OpenPawLabs/diy-guides/bb-lsm6dsv/0-overview/images/battery-1000mah-side-bend-transparent-cropped-img-4592-1.webp

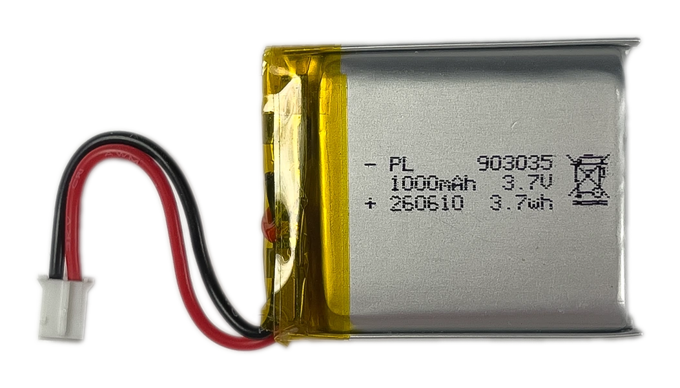
bb-lsm6dsv/0-overview/images/battery-1000mah-side-bend-transparent-cropped-img-4592-1.webp
