OpenPawLabs/diy-guides/bb-lsm6dsv/0-overview/images/battery-1000mah-side-bend-transparent-img-4592.webp

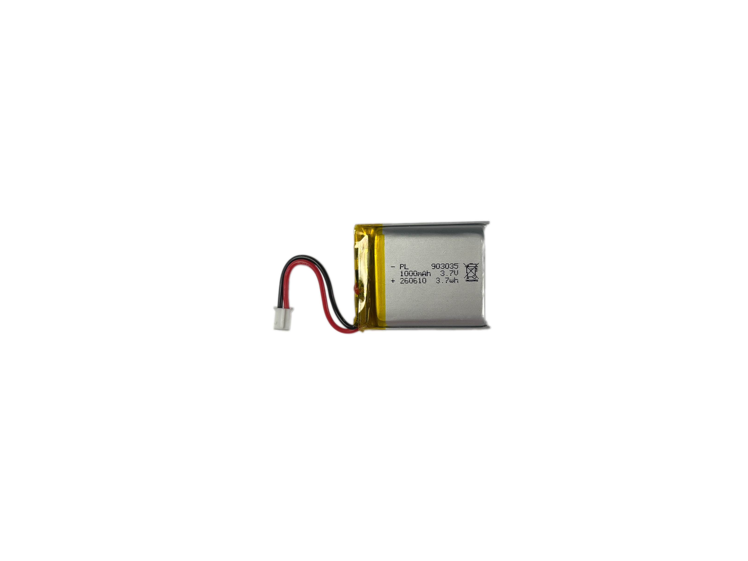
bb-lsm6dsv/0-overview/images/battery-1000mah-side-bend-transparent-img-4592.webp
