OpenPawLabs/diy-guides/bb-lsm6dsv/0-overview/images/body-strap-set-img-4863.webp

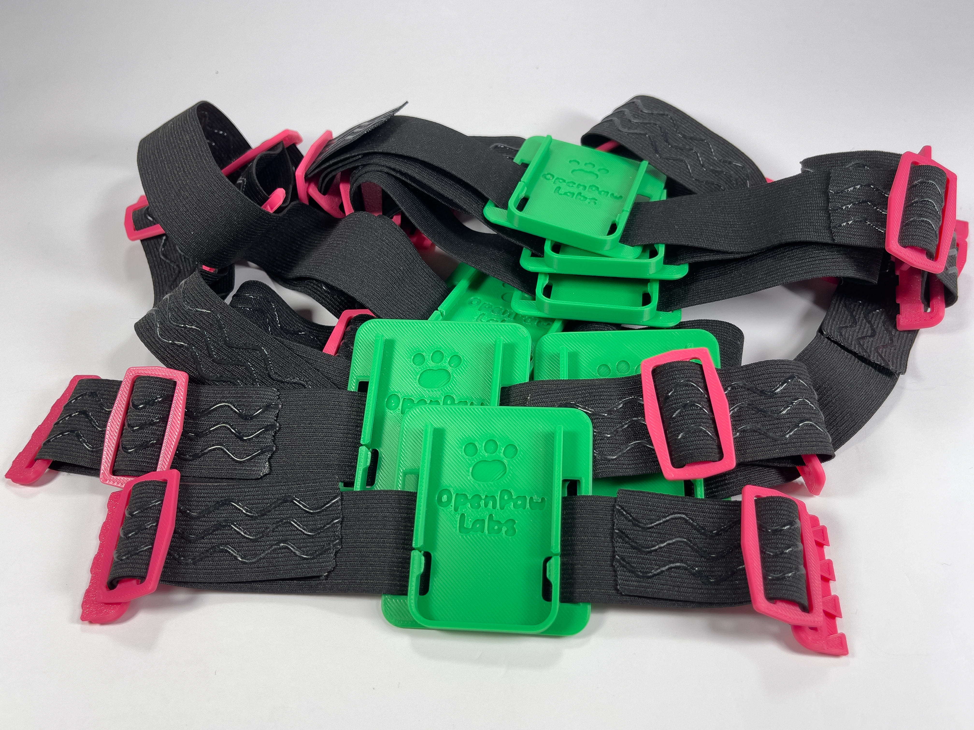
bb-lsm6dsv/0-overview/images/body-strap-set-img-4863.webp
