OpenPawLabs/diy-guides/bb-lsm6dsv/0-overview/images/dock-pcb-transparent-img-4443-1.webp

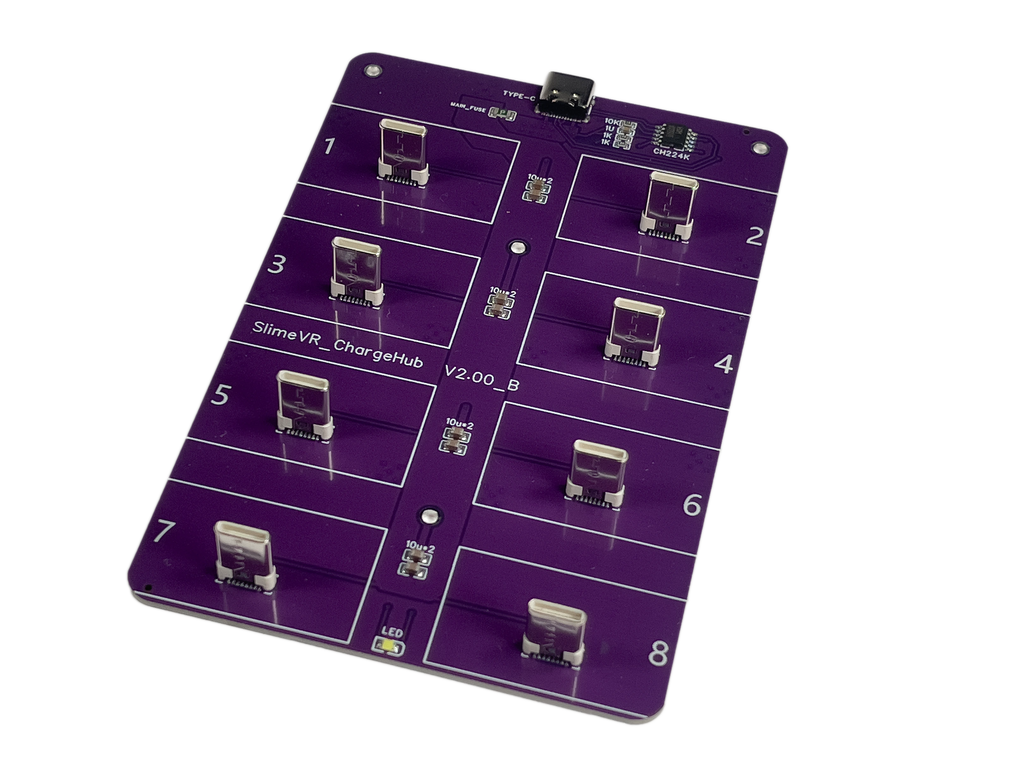
bb-lsm6dsv/0-overview/images/dock-pcb-transparent-img-4443-1.webp
