OpenPawLabs/diy-guides/bb-lsm6dsv/0-overview/images/dock-w-pcb-angled-transparent-img-4545.webp

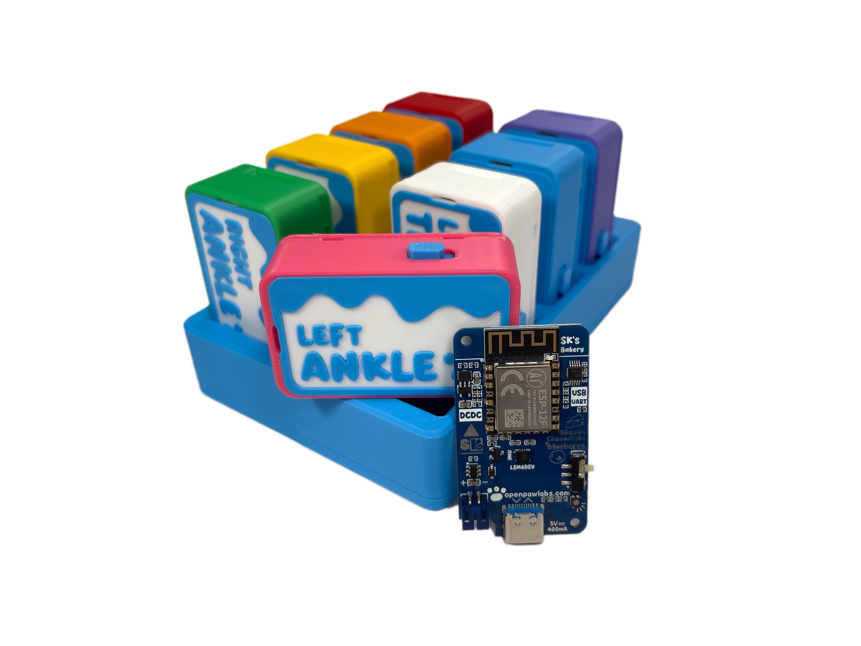
bb-lsm6dsv/0-overview/images/dock-w-pcb-angled-transparent-img-4545.webp
