OpenPawLabs/diy-guides/bb-lsm6dsv/0-overview/images/img-4400-edit.webp

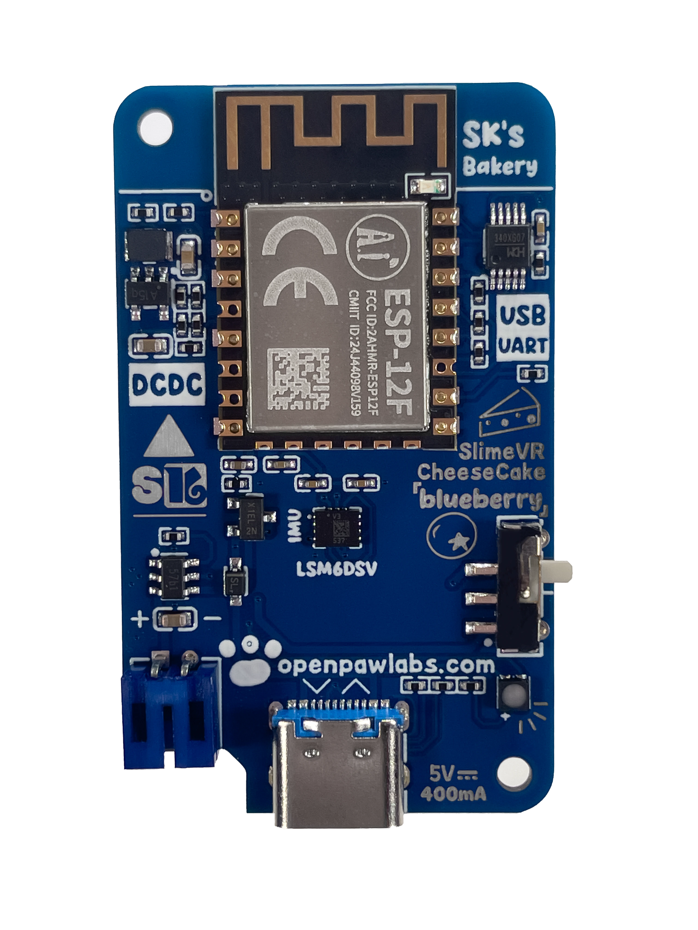
bb-lsm6dsv/0-overview/images/img-4400-edit.webp
