OpenPawLabs/diy-guides/bb-lsm6dsv/0-overview/images/img-4710.webp

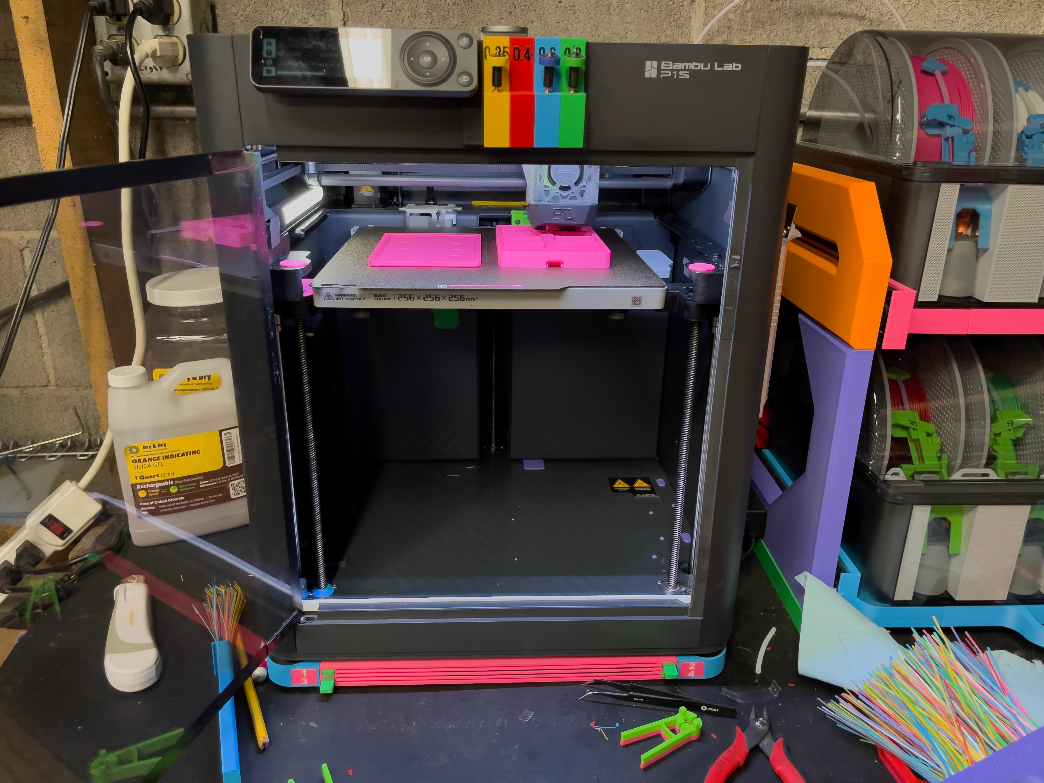
bb-lsm6dsv/0-overview/images/img-4710.webp
