OpenPawLabs/diy-guides/bb-lsm6dsv/0-overview/images/party-face-emoji-big.webp

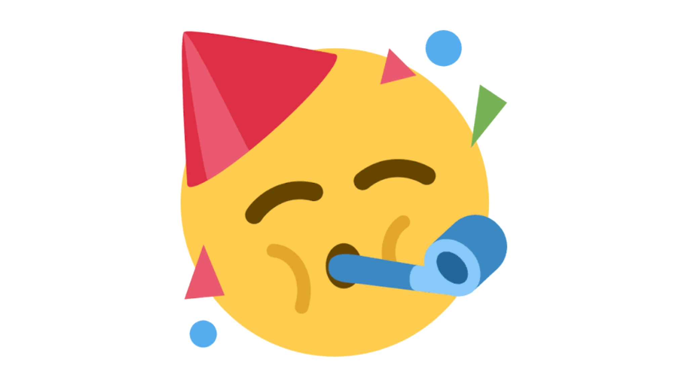
bb-lsm6dsv/0-overview/images/party-face-emoji-big.webp
