OpenPawLabs/diy-guides/bb-lsm6dsv/0-overview/images/tracker-board-transparent-1080.webp

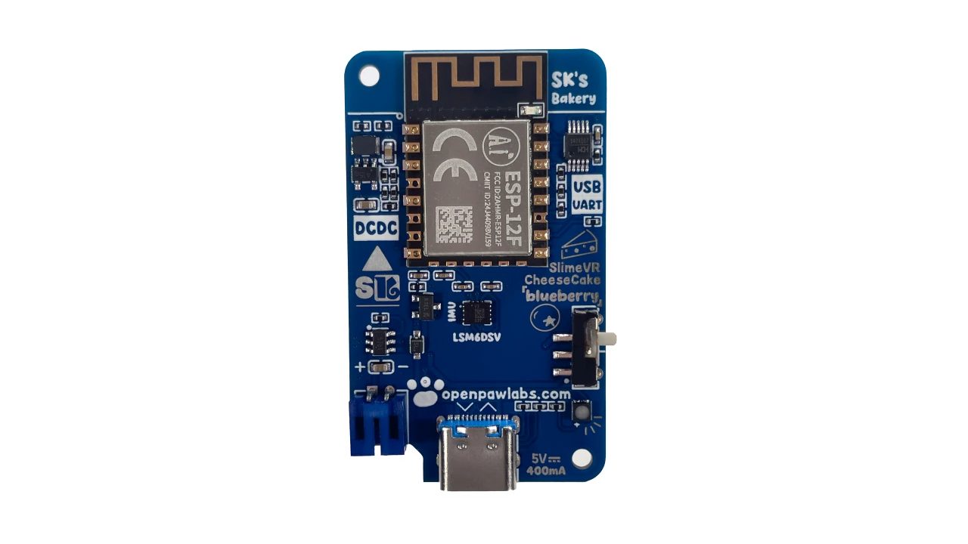
bb-lsm6dsv/0-overview/images/tracker-board-transparent-1080.webp
