OpenPawLabs/diy-guides/bb-lsm6dsv/0-overview/images/vyrovr-comfort-straps.webp

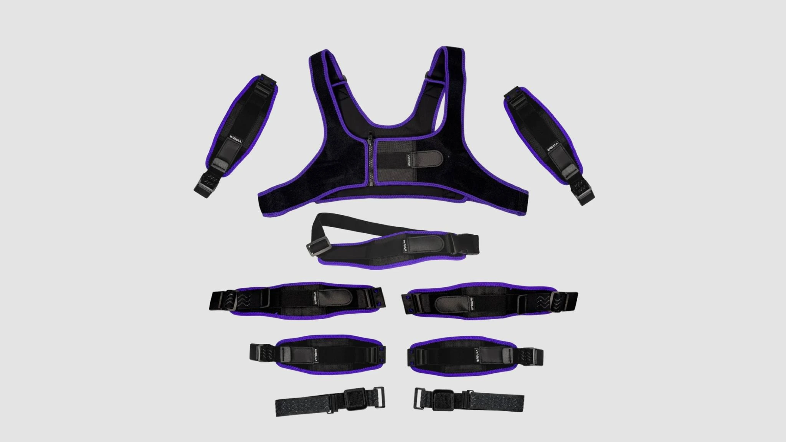
bb-lsm6dsv/0-overview/images/vyrovr-comfort-straps.webp
