OpenPawLabs/diy-guides/bb-lsm6dsv/diy-straps/images/chest-strap-3-ways-img-4871.webp

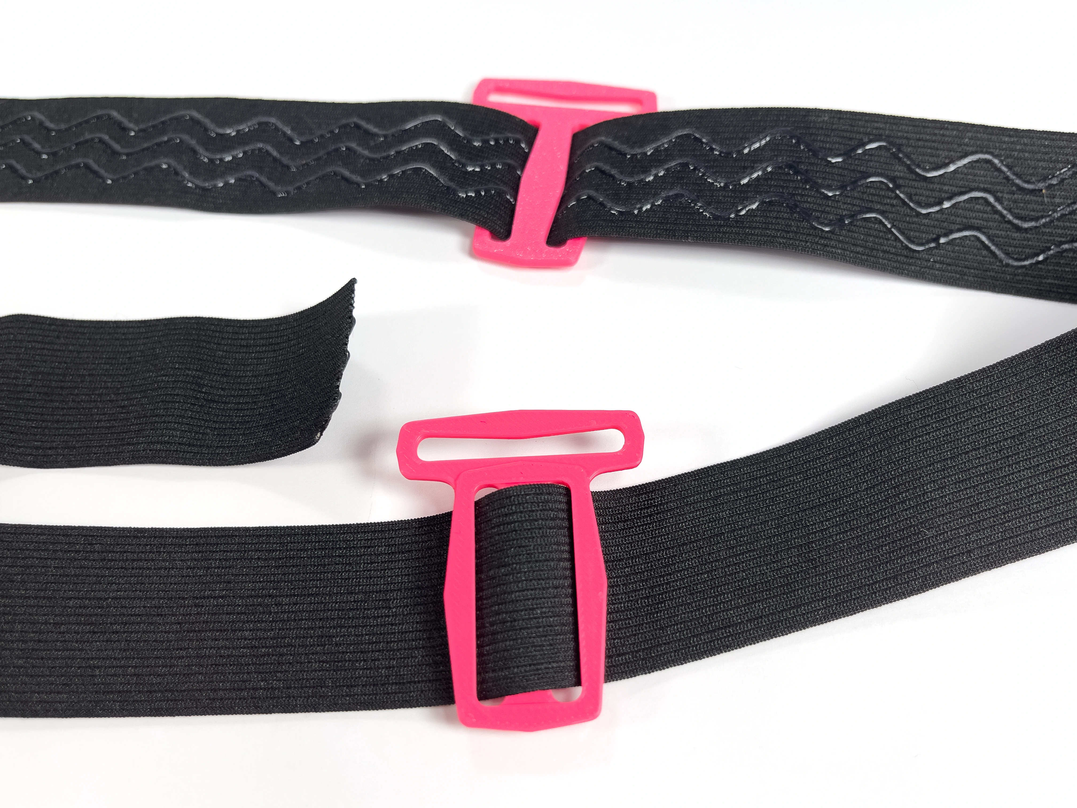
bb-lsm6dsv/diy-straps/images/chest-strap-3-ways-img-4871.webp
