OpenPawLabs/diy-guides/bb-lsm6dsv/diy-straps/images/chest-strap-3-ways-pt2-img-4873.webp

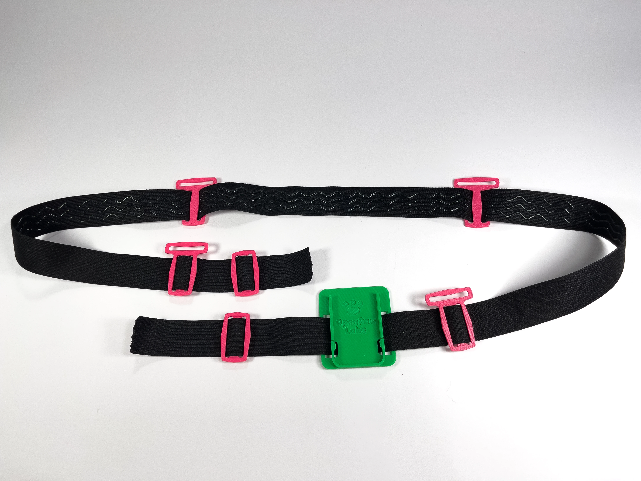
bb-lsm6dsv/diy-straps/images/chest-strap-3-ways-pt2-img-4873.webp
