OpenPawLabs/diy-guides/bb-lsm6dsv/diy-straps/images/chest-strap-balance-img-4874.webp

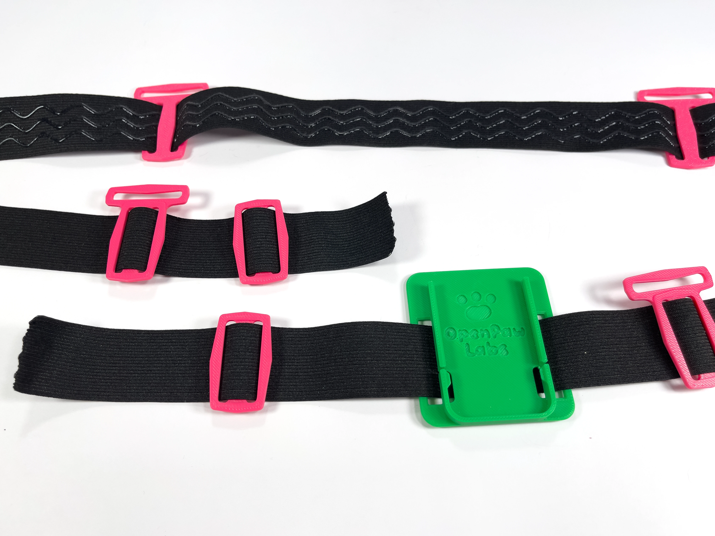
bb-lsm6dsv/diy-straps/images/chest-strap-balance-img-4874.webp
