OpenPawLabs/diy-guides/bb-lsm6dsv/diy-straps/images/chest-strap-clasps-img-4879.webp

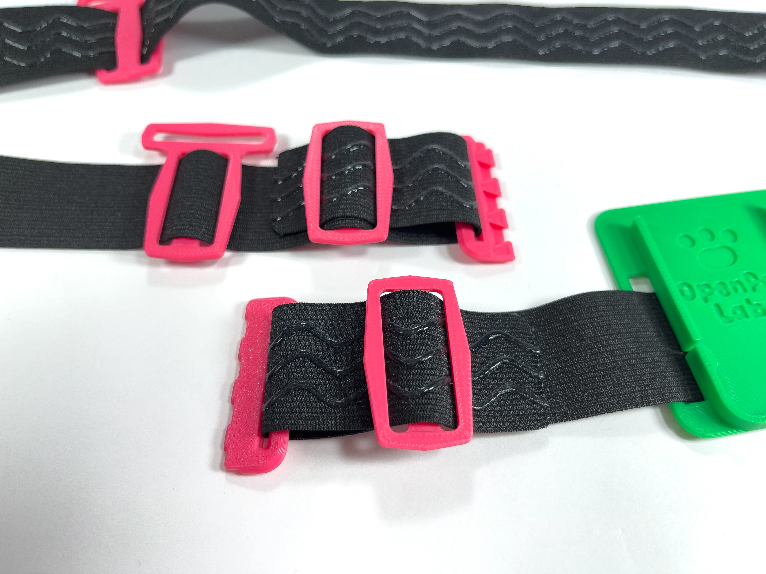
bb-lsm6dsv/diy-straps/images/chest-strap-clasps-img-4879.webp
