OpenPawLabs/diy-guides/bb-lsm6dsv/diy-straps/images/chest-straps-cut-to-length-img-4866-2.webp

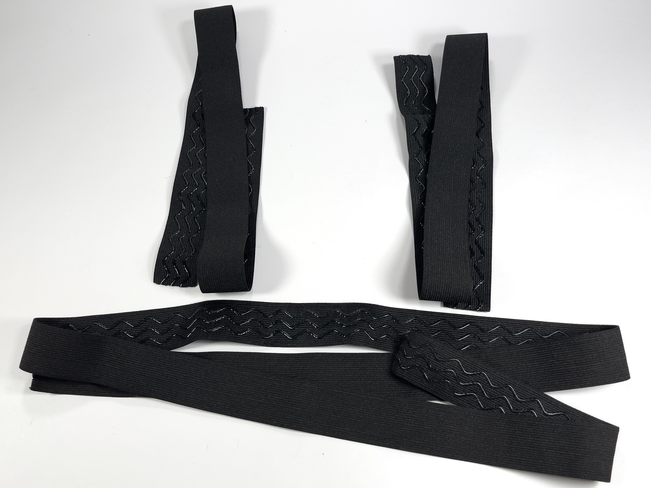
bb-lsm6dsv/diy-straps/images/chest-straps-cut-to-length-img-4866-2.webp
