OpenPawLabs/diy-guides/bb-lsm6dsv/diy-straps/images/chest-straps-pt1-img-4870.webp

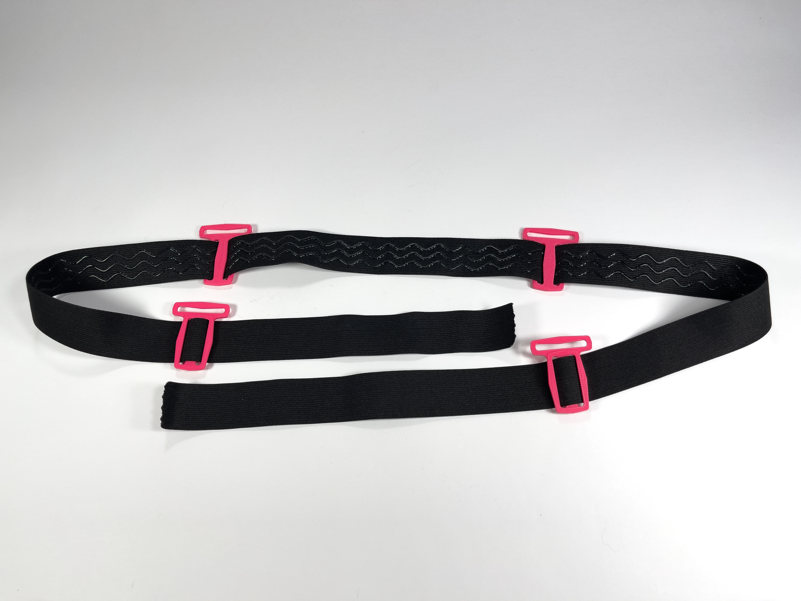
bb-lsm6dsv/diy-straps/images/chest-straps-pt1-img-4870.webp
