OpenPawLabs/diy-guides/bb-lsm6dsv/diy-straps/images/clasp-alignment-img-4828.webp

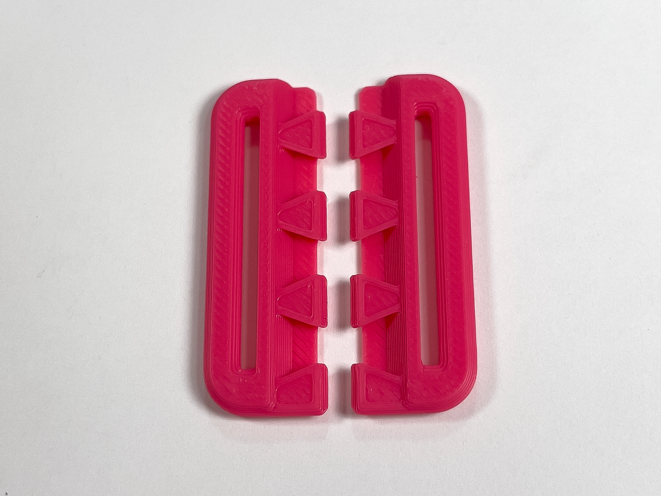
bb-lsm6dsv/diy-straps/images/clasp-alignment-img-4828.webp
