OpenPawLabs/diy-guides/bb-lsm6dsv/diy-straps/images/clasps-together-img-4861.webp

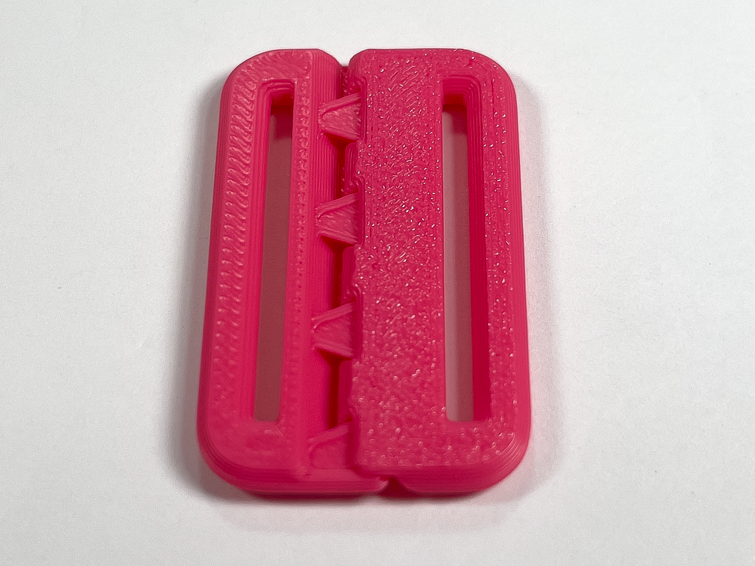
bb-lsm6dsv/diy-straps/images/clasps-together-img-4861.webp
