OpenPawLabs/diy-guides/bb-lsm6dsv/diy-straps/images/cut-to-length-img-4819.webp

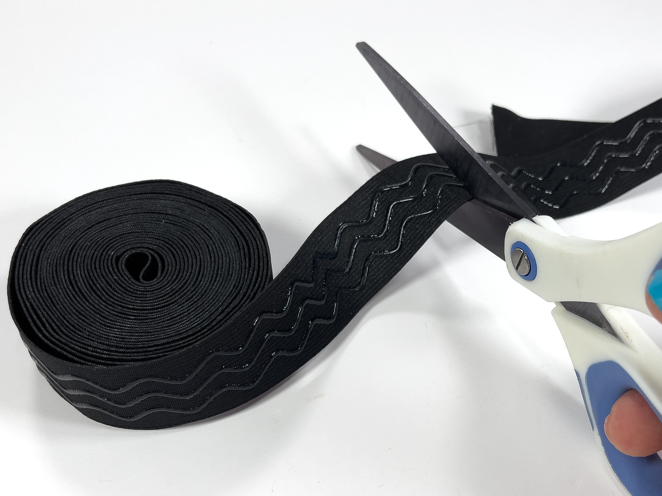
bb-lsm6dsv/diy-straps/images/cut-to-length-img-4819.webp
