OpenPawLabs/diy-guides/bb-lsm6dsv/diy-straps/images/diy-strap-set-img-4812.webp

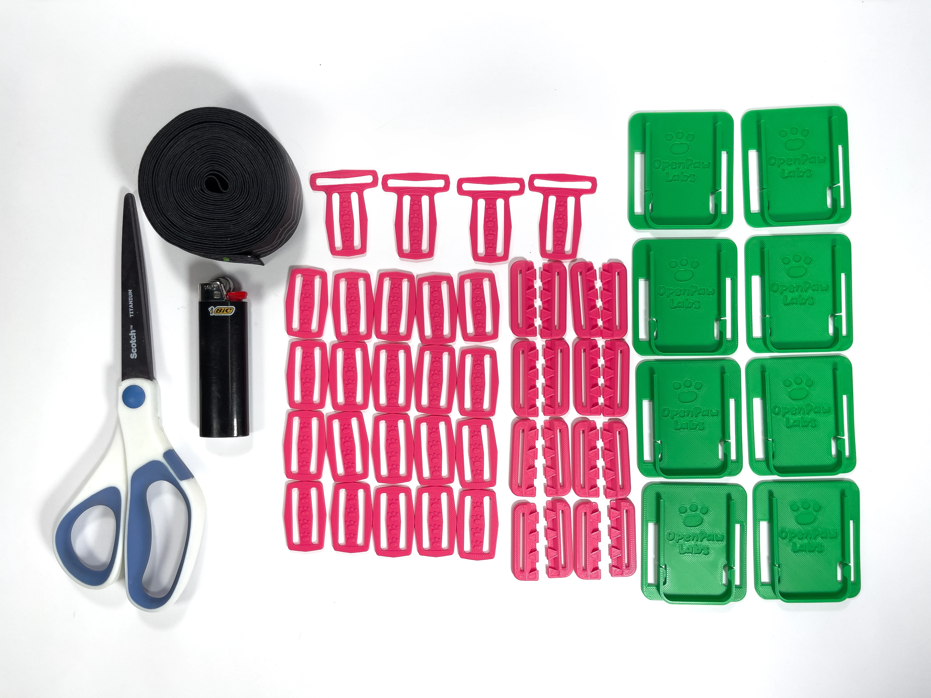
bb-lsm6dsv/diy-straps/images/diy-strap-set-img-4812.webp
