OpenPawLabs/diy-guides/bb-lsm6dsv/diy-straps/images/extra-strap-length-img-4814.webp

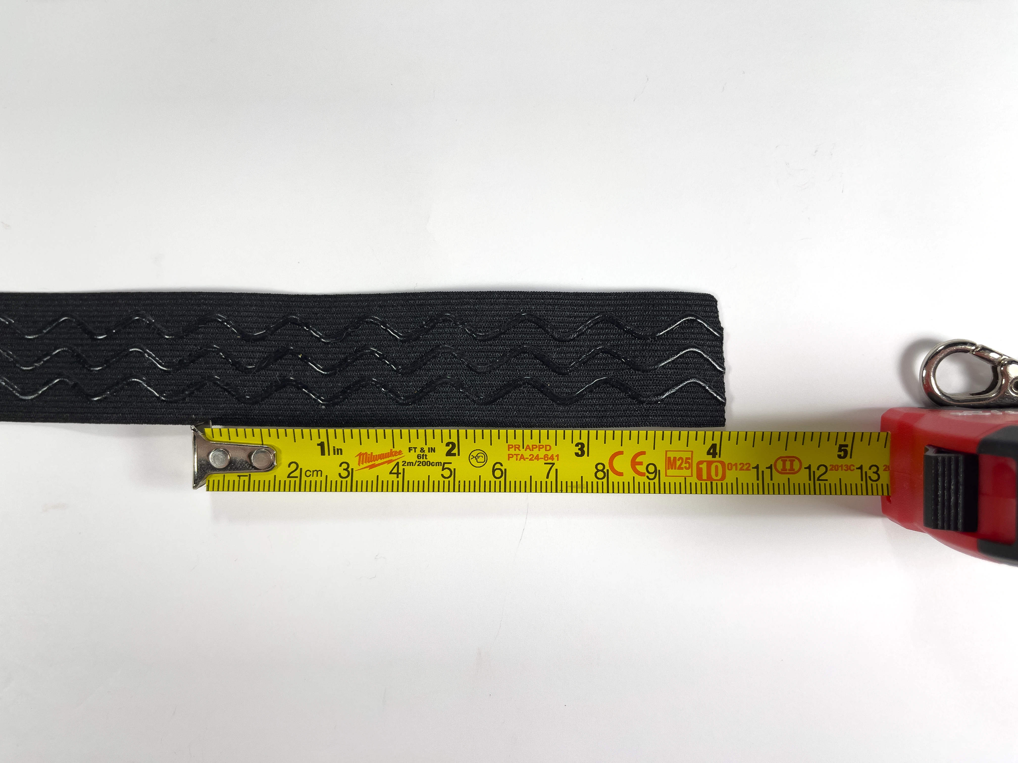
bb-lsm6dsv/diy-straps/images/extra-strap-length-img-4814.webp
