OpenPawLabs/diy-guides/bb-lsm6dsv/diy-straps/images/full-chest-strap-img-4892.webp

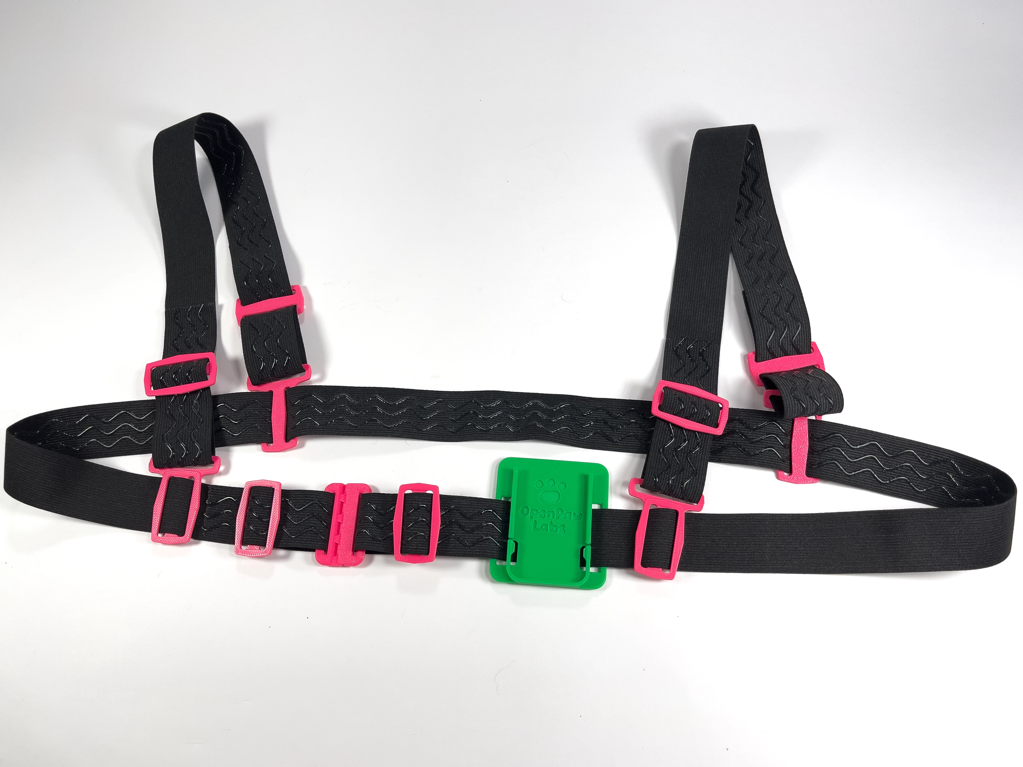
bb-lsm6dsv/diy-straps/images/full-chest-strap-img-4892.webp
