OpenPawLabs/diy-guides/bb-lsm6dsv/diy-straps/images/full-shoulder-strap-side-img-4889.webp

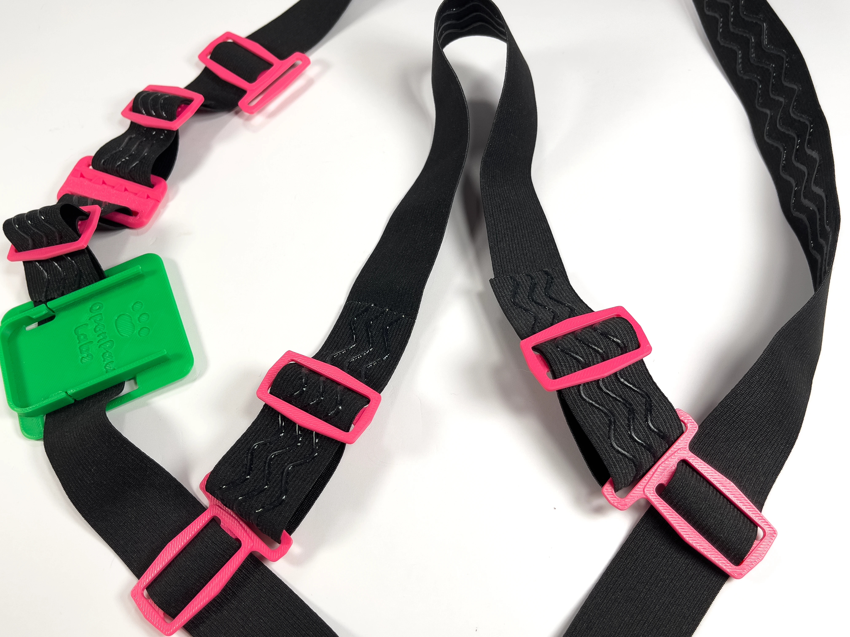
bb-lsm6dsv/diy-straps/images/full-shoulder-strap-side-img-4889.webp
