OpenPawLabs/diy-guides/bb-lsm6dsv/diy-straps/images/full-shoulder-strap-top-view-img-4890.webp

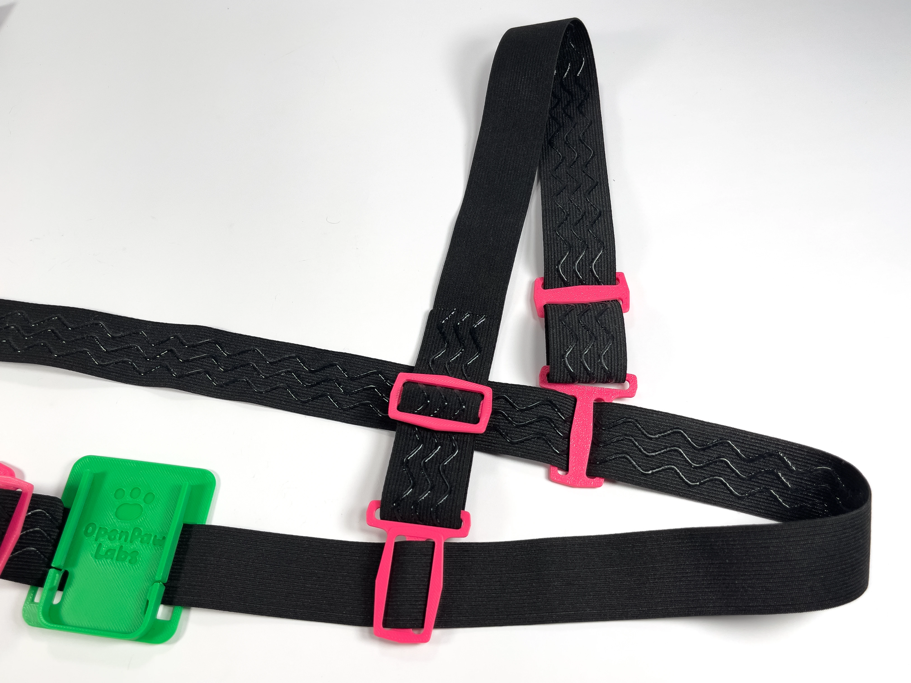
bb-lsm6dsv/diy-straps/images/full-shoulder-strap-top-view-img-4890.webp
