OpenPawLabs/diy-guides/bb-lsm6dsv/diy-straps/images/full-strap-set-img-4894.webp

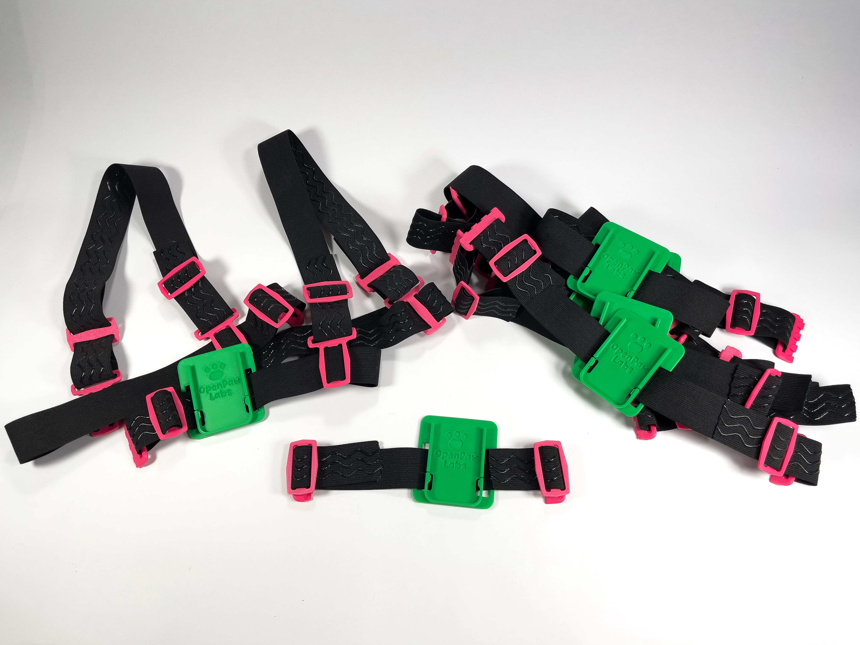
bb-lsm6dsv/diy-straps/images/full-strap-set-img-4894.webp
