OpenPawLabs/diy-guides/bb-lsm6dsv/diy-straps/images/shoulder-strap-img-4882.webp

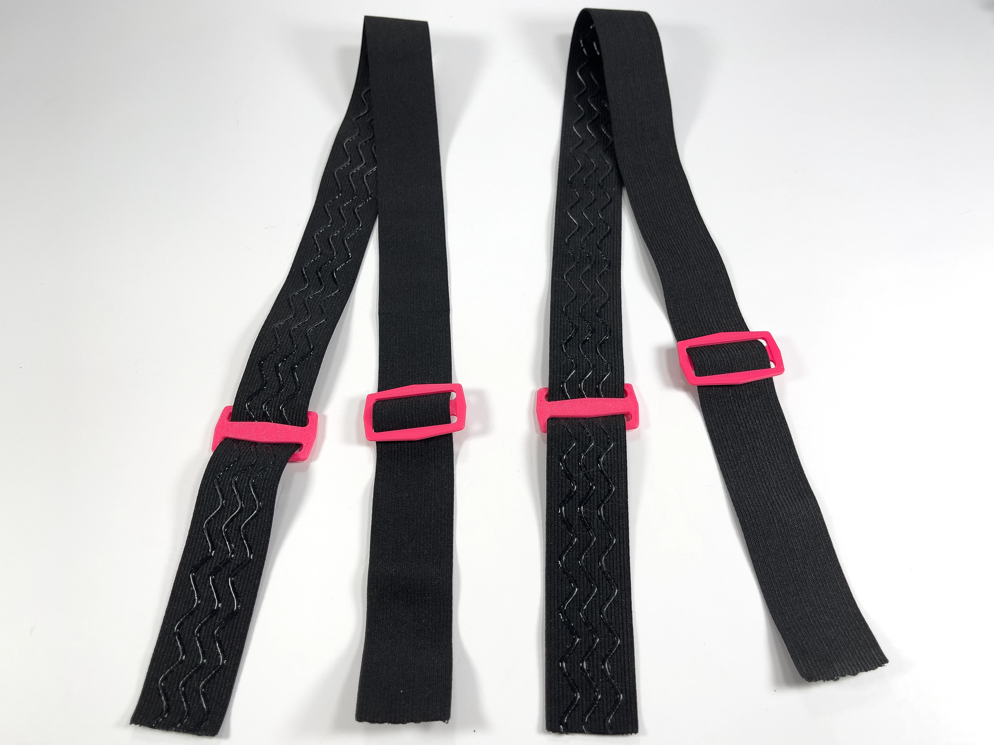
bb-lsm6dsv/diy-straps/images/shoulder-strap-img-4882.webp
