OpenPawLabs/diy-guides/bb-lsm6dsv/diy-straps/images/shoulder-strap-threading-pt1-img-4884.webp

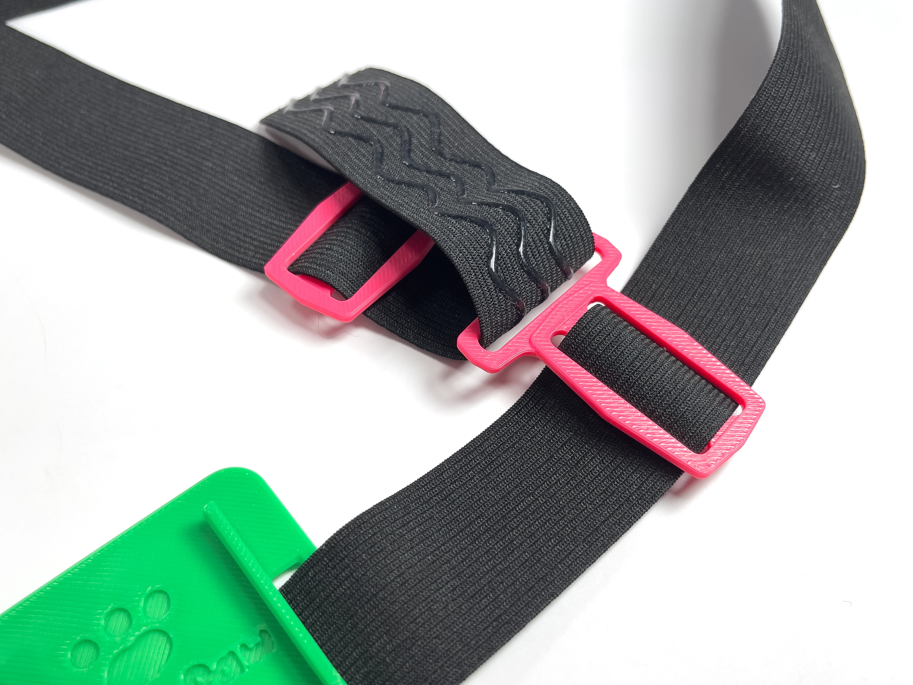
bb-lsm6dsv/diy-straps/images/shoulder-strap-threading-pt1-img-4884.webp
