OpenPawLabs/diy-guides/bb-lsm6dsv/diy-straps/images/shoulder-strap-threading-pt2-img-4886.webp

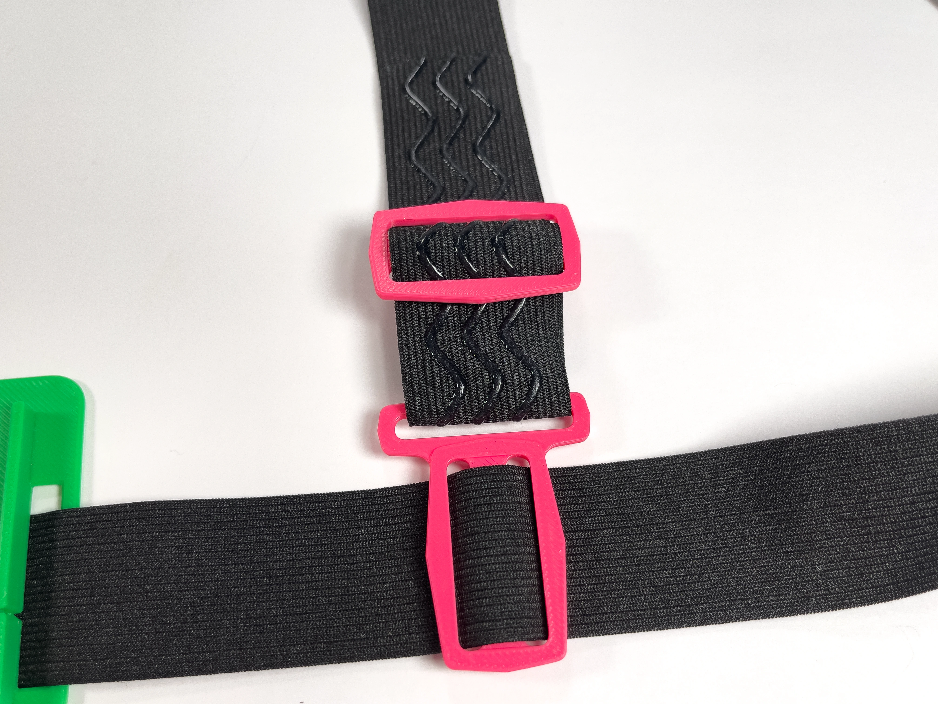
bb-lsm6dsv/diy-straps/images/shoulder-strap-threading-pt2-img-4886.webp
