OpenPawLabs/diy-guides/bb-lsm6dsv/diy-straps/images/strap-balance-closeup-img-4875.webp

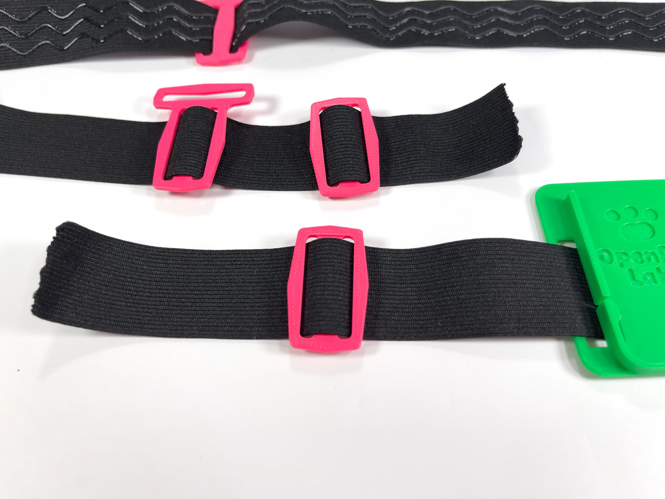
bb-lsm6dsv/diy-straps/images/strap-balance-closeup-img-4875.webp
