OpenPawLabs/diy-guides/bb-lsm6dsv/diy-straps/images/strap-clasp-threading-pt1-img-4844.webp

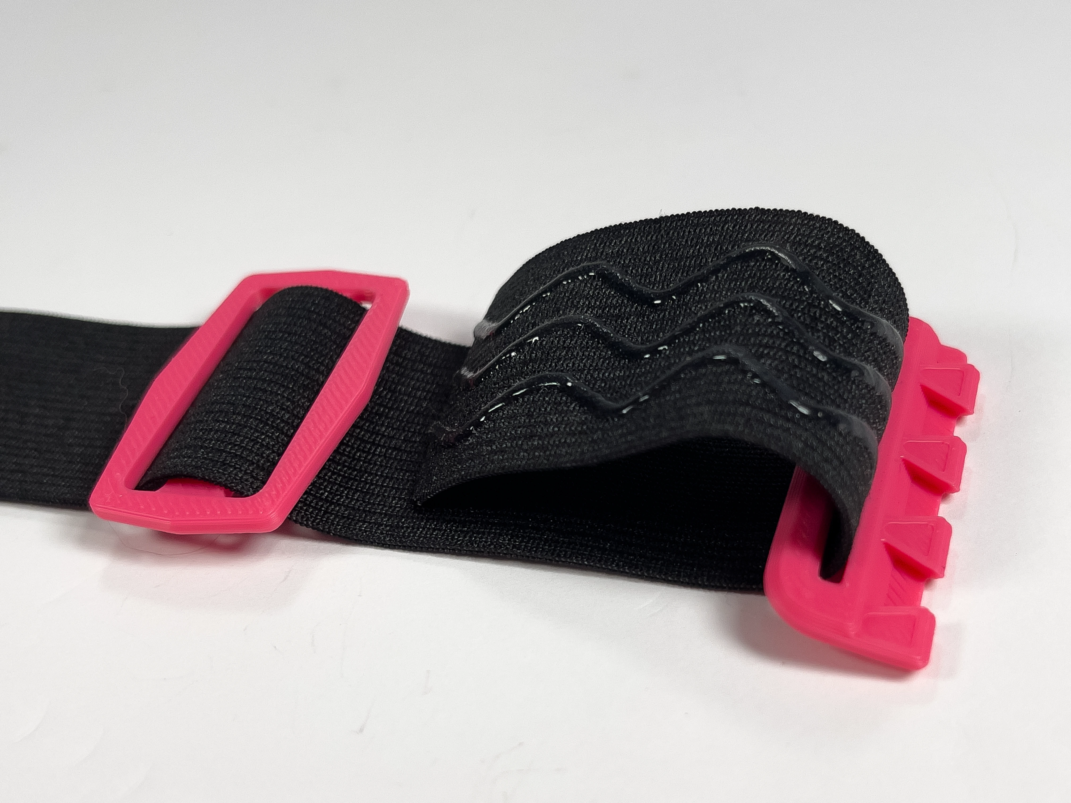
bb-lsm6dsv/diy-straps/images/strap-clasp-threading-pt1-img-4844.webp
