OpenPawLabs/diy-guides/bb-lsm6dsv/diy-straps/images/strap-clasp-two-img-4852.webp

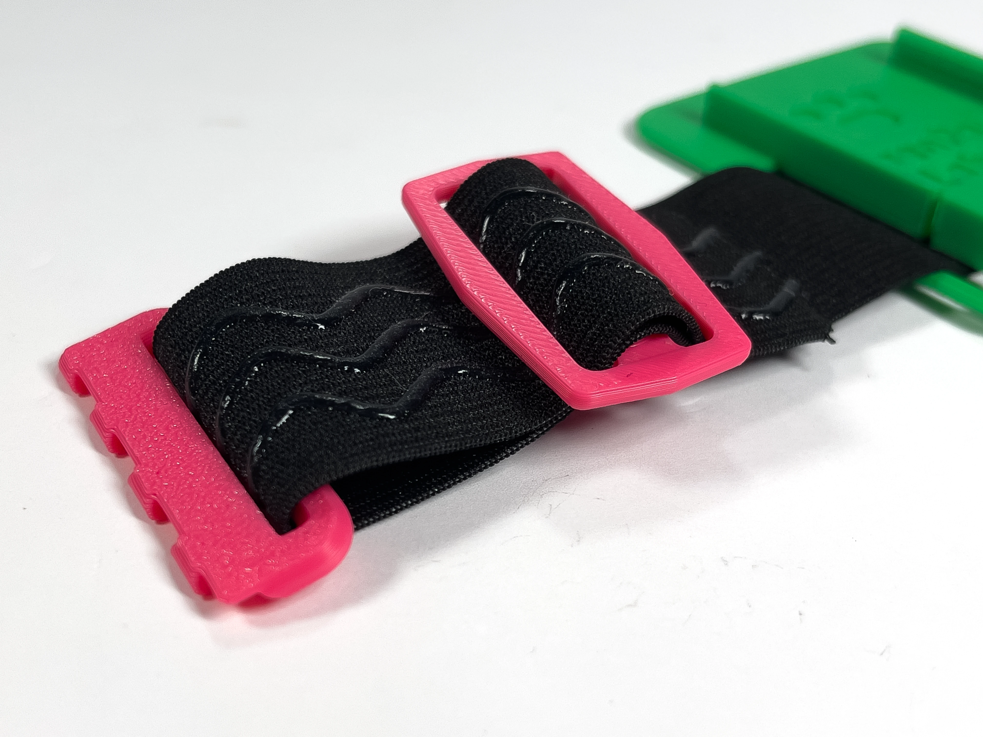
bb-lsm6dsv/diy-straps/images/strap-clasp-two-img-4852.webp
