OpenPawLabs/diy-guides/bb-lsm6dsv/diy-straps/images/strap-cut-to-length-frayed-img-4822.webp

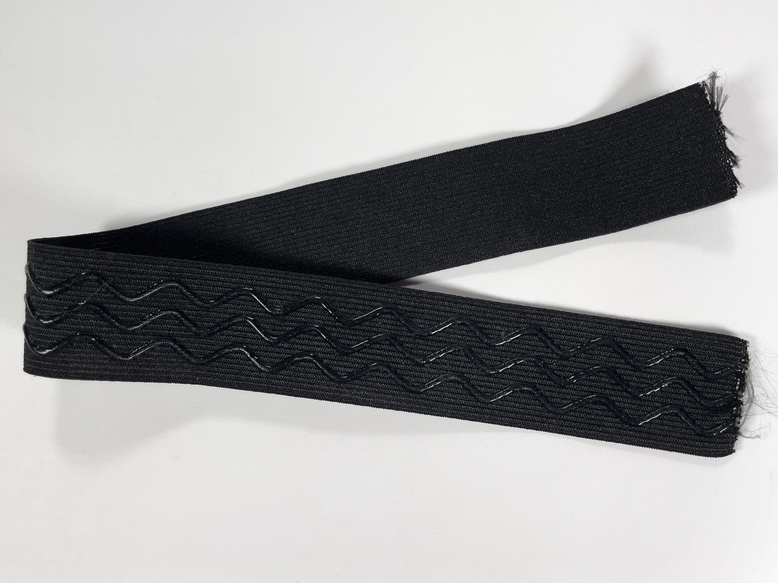
bb-lsm6dsv/diy-straps/images/strap-cut-to-length-frayed-img-4822.webp
