OpenPawLabs/diy-guides/bb-lsm6dsv/diy-straps/images/strap-standing-img-4857.webp

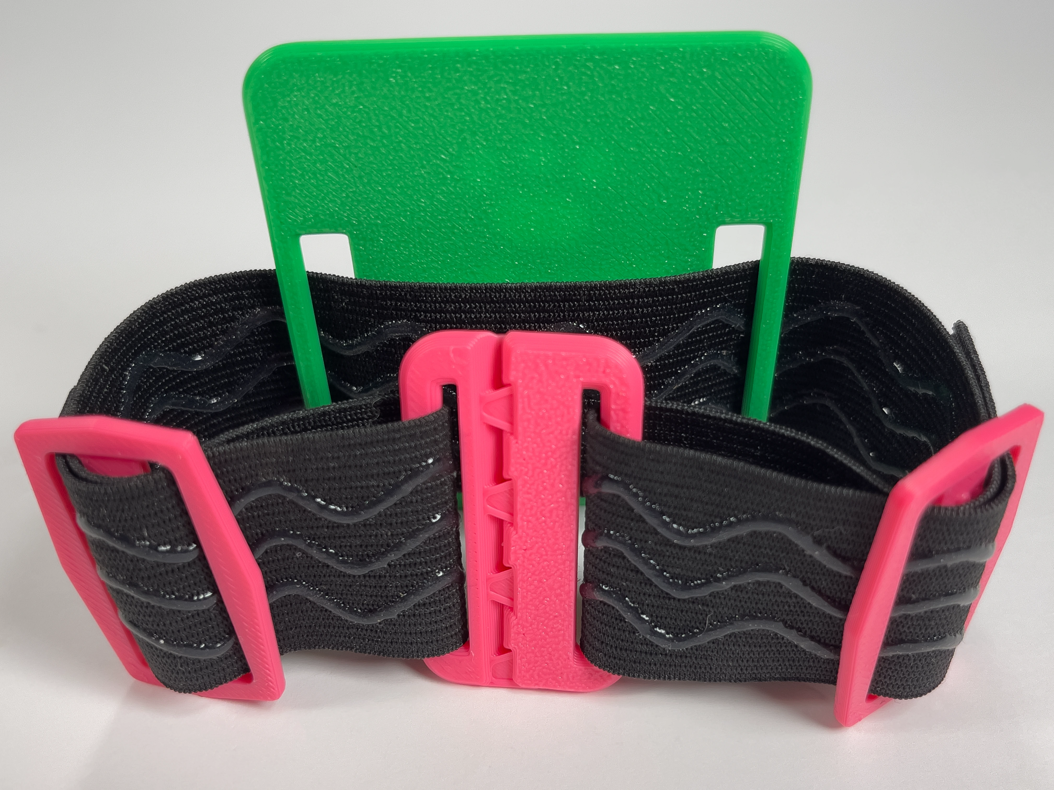
bb-lsm6dsv/diy-straps/images/strap-standing-img-4857.webp
