OpenPawLabs/diy-guides/bb-lsm6dsv/diy-straps/images/strap-threading-img-4850.webp

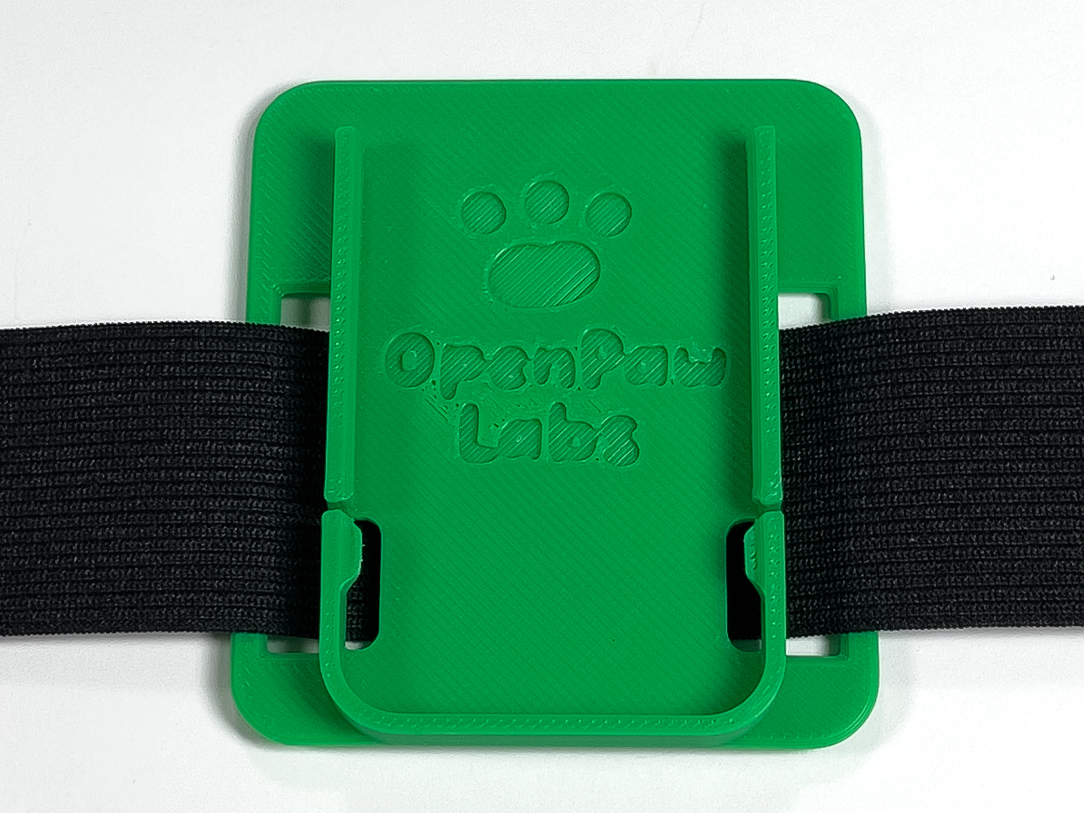
bb-lsm6dsv/diy-straps/images/strap-threading-img-4850.webp
