OpenPawLabs/diy-guides/bb-lsm6dsv/diy-straps/images/strap-threading-pt1-img-4834.webp

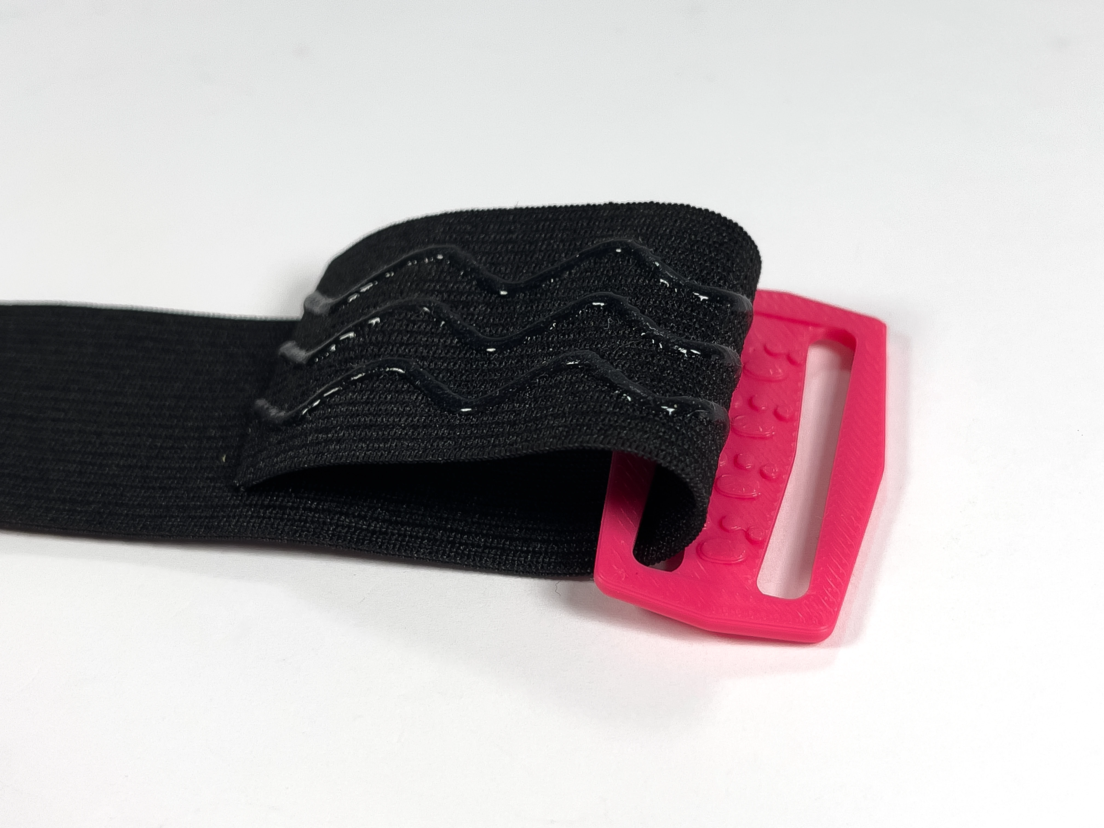
bb-lsm6dsv/diy-straps/images/strap-threading-pt1-img-4834.webp
