OpenPawLabs/diy-guides/bb-lsm6dsv/diy-straps/images/strap-threading-pt2-img-4839.webp

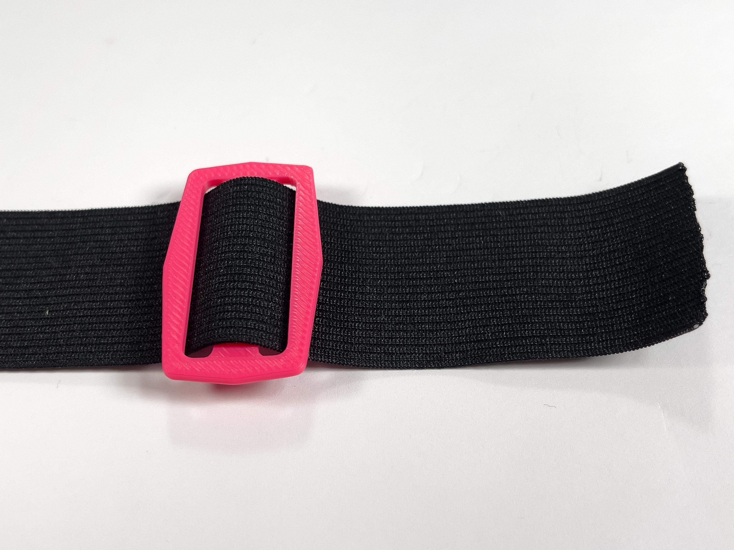
bb-lsm6dsv/diy-straps/images/strap-threading-pt2-img-4839.webp
