OpenPawLabs/diy-guides/bb-lsm6dsv/diy-straps/images/strap-threading-pt3-img-4845.webp

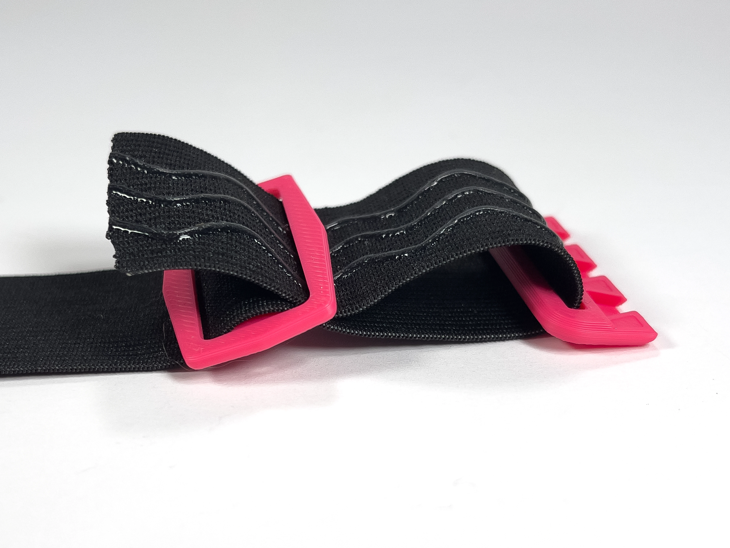
bb-lsm6dsv/diy-straps/images/strap-threading-pt3-img-4845.webp
