OpenPawLabs/diy-guides/bb-lsm6dsv/diy-straps/images/strap-threading-pt4img-4846.webp

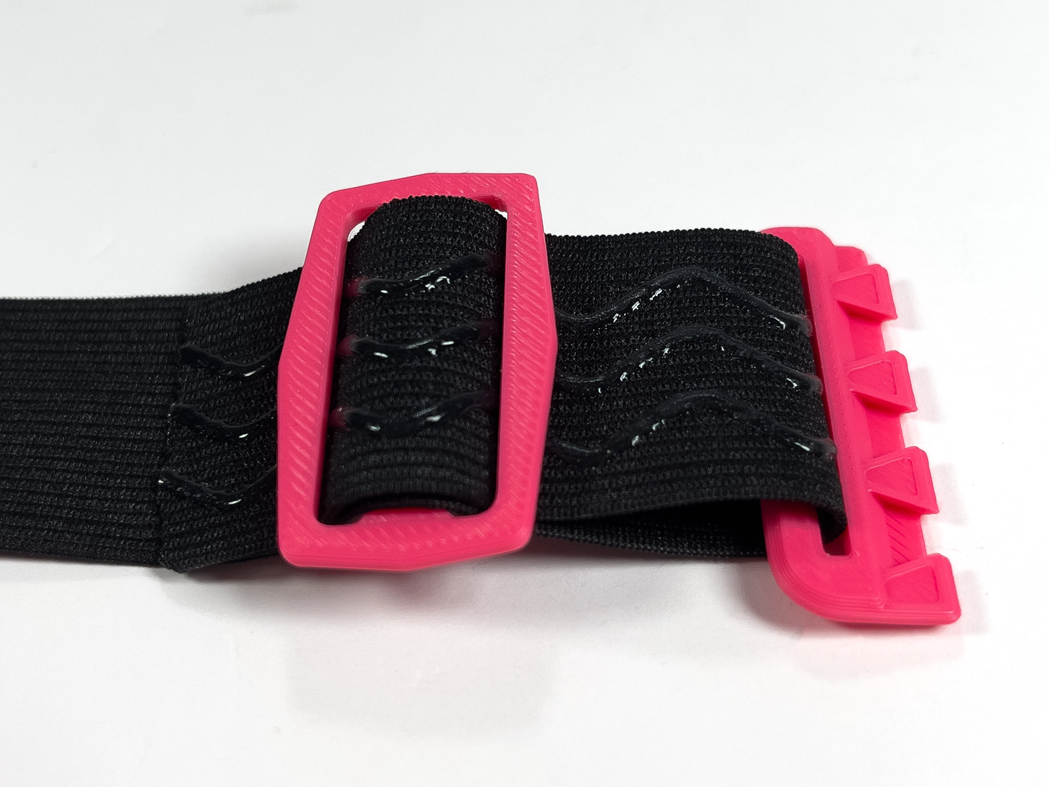
bb-lsm6dsv/diy-straps/images/strap-threading-pt4img-4846.webp
