OpenPawLabs/diy-guides/bb-lsm6dsv/diy-straps/images/sull-strap-img-4854.webp

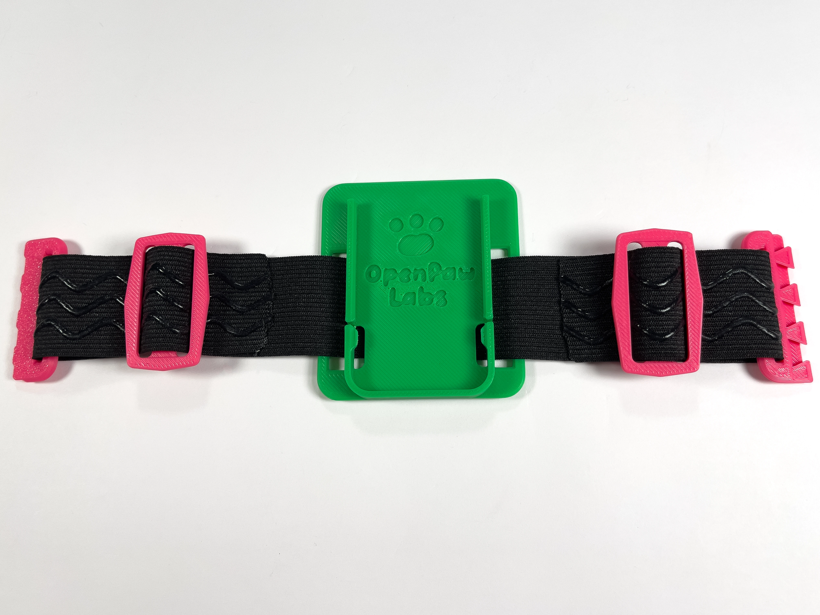
bb-lsm6dsv/diy-straps/images/sull-strap-img-4854.webp
