OpenPawLabs/diy-guides/bb-lsm6dsv/diy-straps/images/thread-strap-mount-img-4849.webp

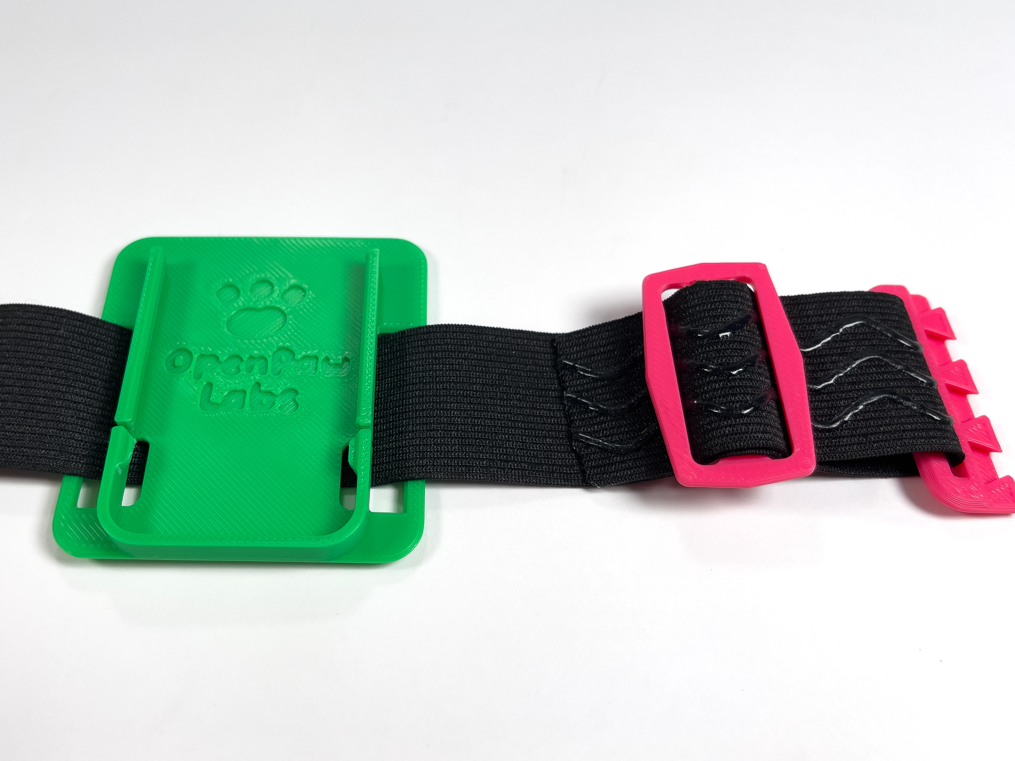
bb-lsm6dsv/diy-straps/images/thread-strap-mount-img-4849.webp
