OpenPawLabs/diy-guides/bb-lsm6dsv/diy-straps/images/tighten-straps-img-4858.webp

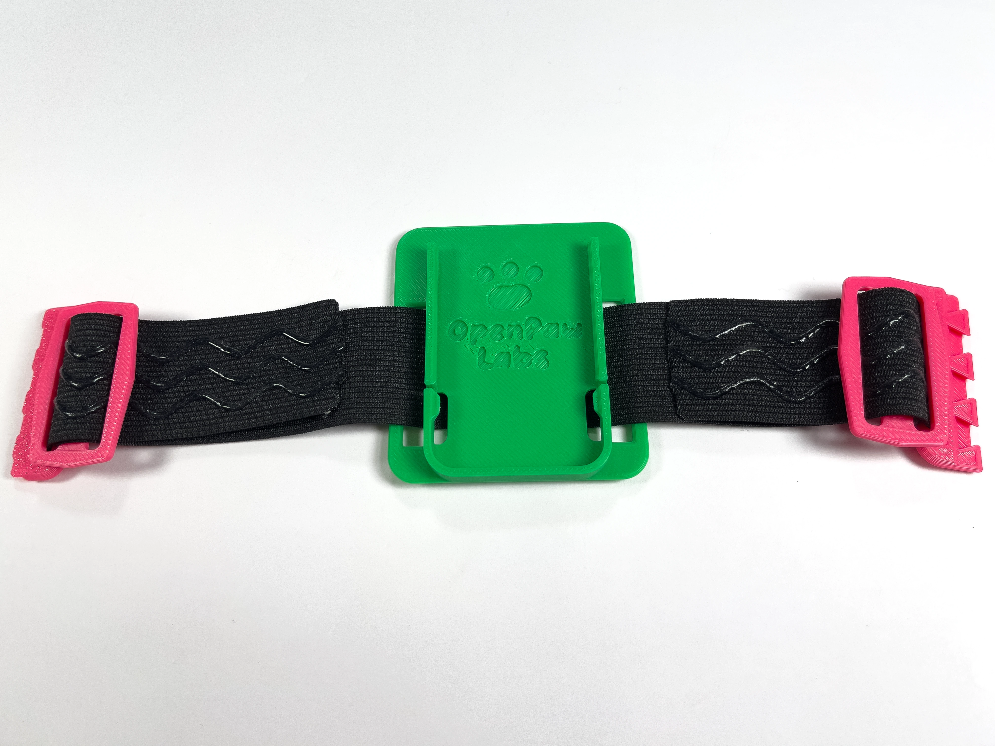
bb-lsm6dsv/diy-straps/images/tighten-straps-img-4858.webp
