OpenPawLabs/diy-guides/bb-lsm6dsv/diy-straps/images/wrapped-strap-img-4815.webp

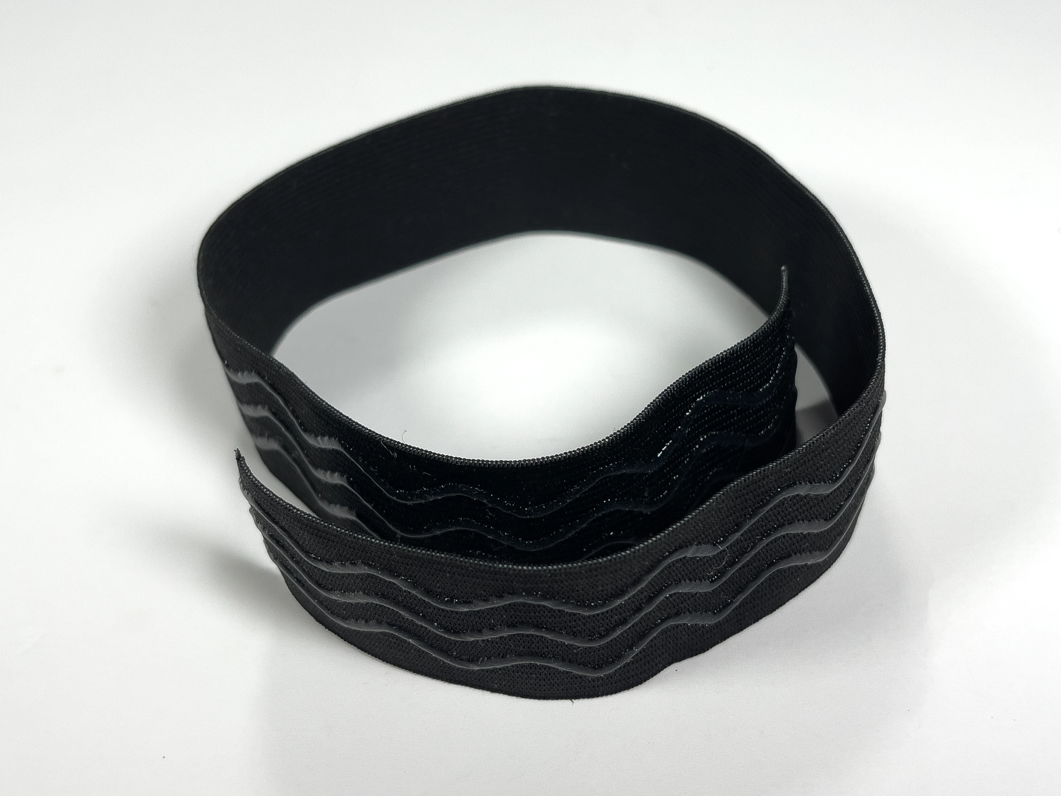
bb-lsm6dsv/diy-straps/images/wrapped-strap-img-4815.webp
