OpenPawLabs/diy-guides/common/1-vrchat-use/images/img-4655.webp

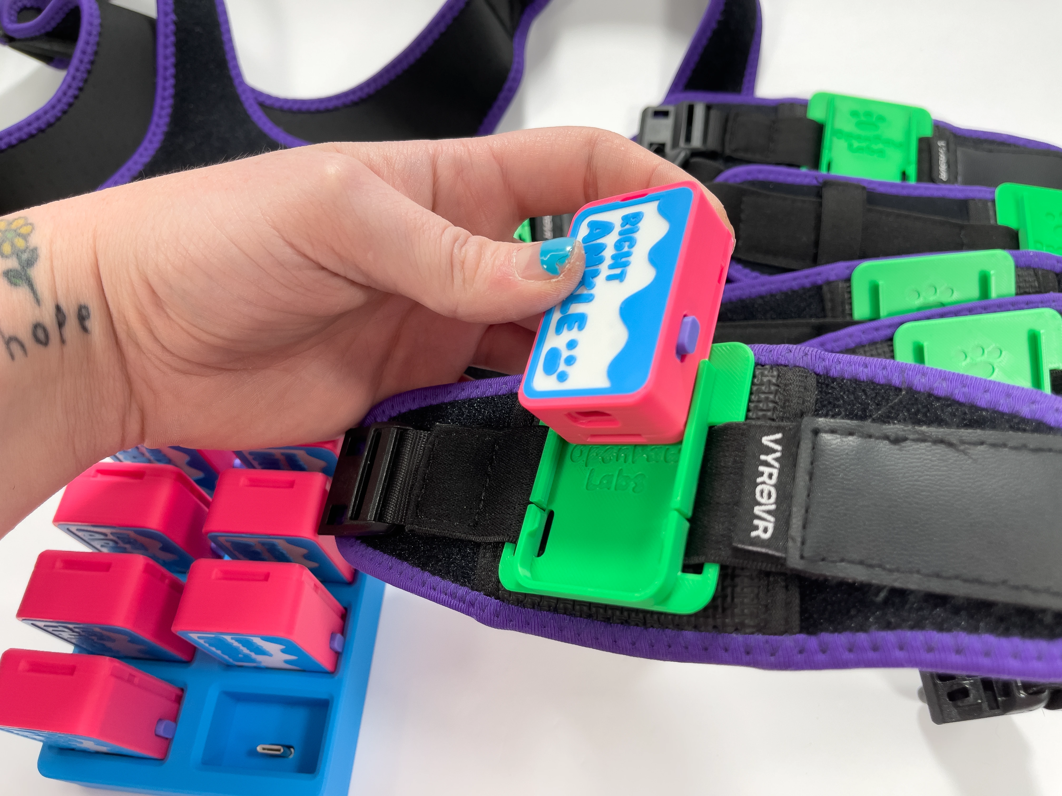
common/1-vrchat-use/images/img-4655.webp
