OpenPawLabs/diy-guides/common/1-vrchat-use/images/tracker-orientation-1.webp

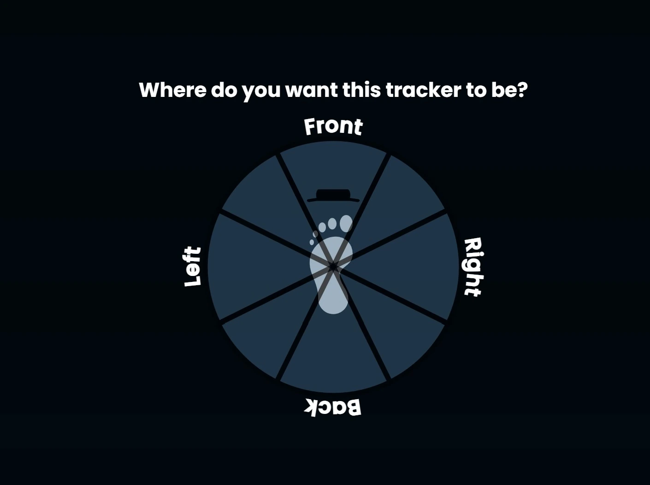
common/1-vrchat-use/images/tracker-orientation-1.webp
