OpenPawLabs/diy-guides/common/1-vrchat-use/images/tracker-settings.webp

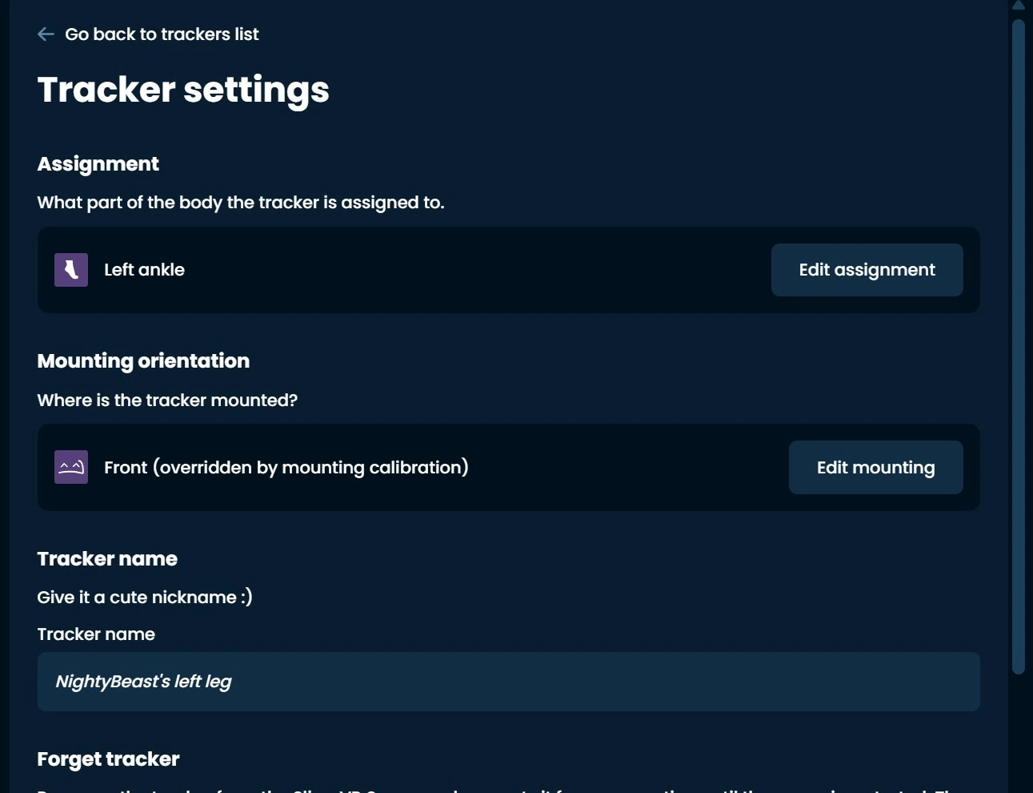
common/1-vrchat-use/images/tracker-settings.webp
