OpenPawLabs/diy-guides/common/1-vrchat-use/images/vrchat-wave.webp

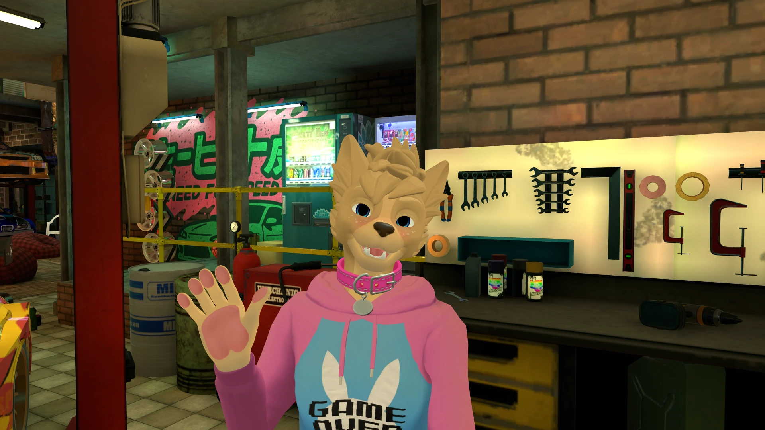
common/1-vrchat-use/images/vrchat-wave.webp
