OpenPawLabs/diy-guides/bb-lsm6dsv/diy-straps/images/chest-strap-parts-img-4869-1.webp

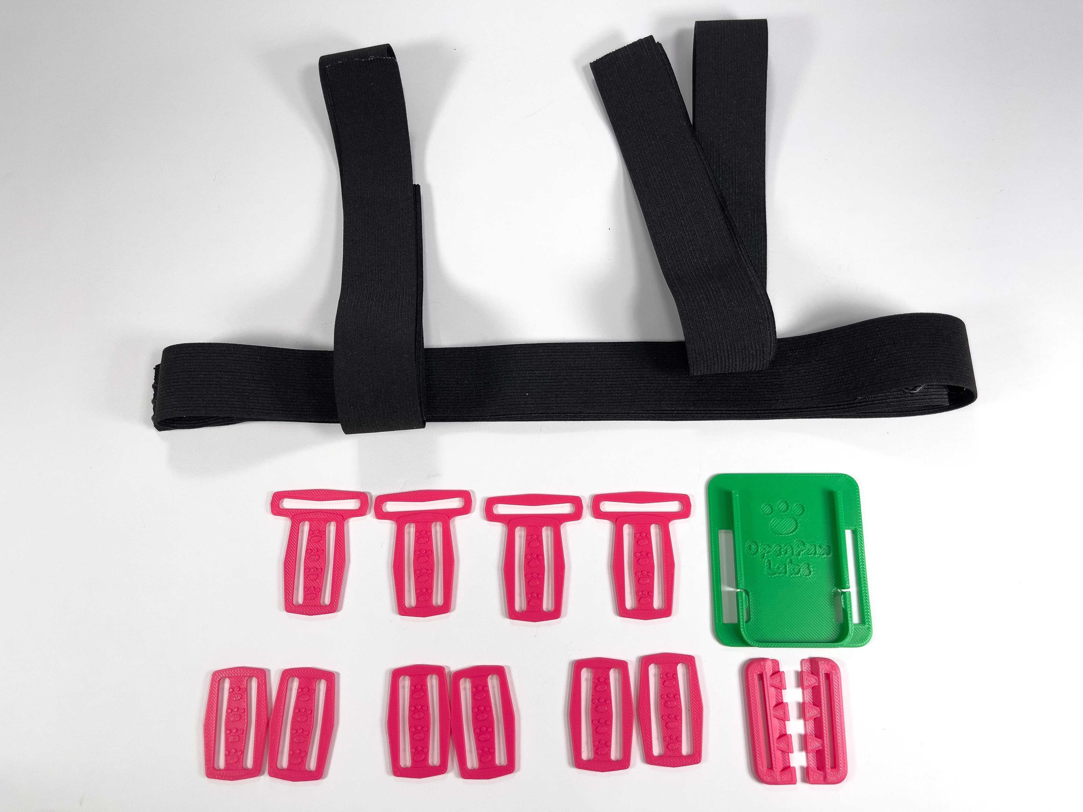
bb-lsm6dsv/diy-straps/images/chest-strap-parts-img-4869-1.webp
