OpenPawLabs/diy-guides/bb-lsm6dsv/diy-straps/images/roll-of-material-img-4818.webp

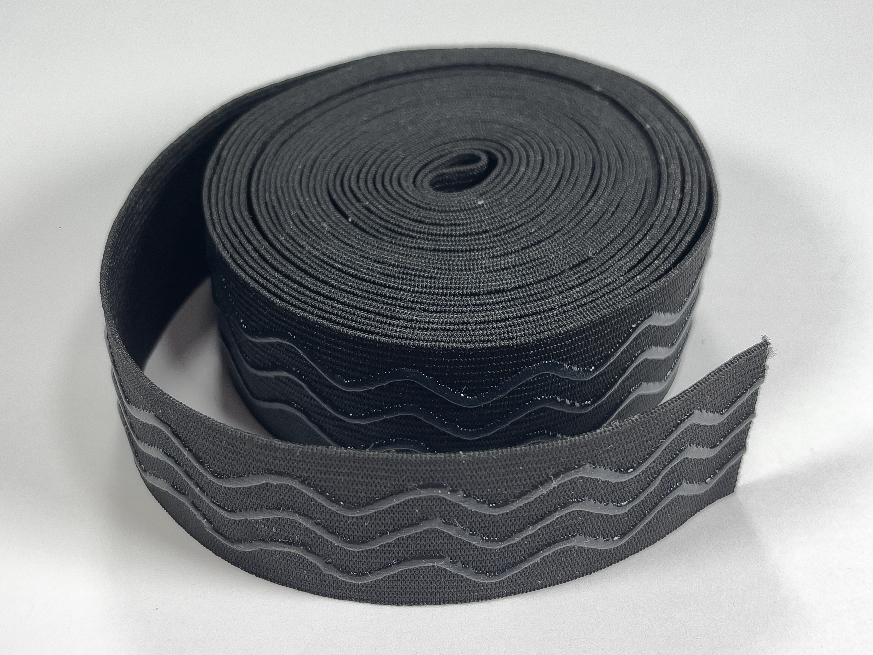
bb-lsm6dsv/diy-straps/images/roll-of-material-img-4818.webp
