OpenPawLabs/diy-guides/bb-lsm6dsv/diy-straps/images/strap-and-parts-img-4830.webp

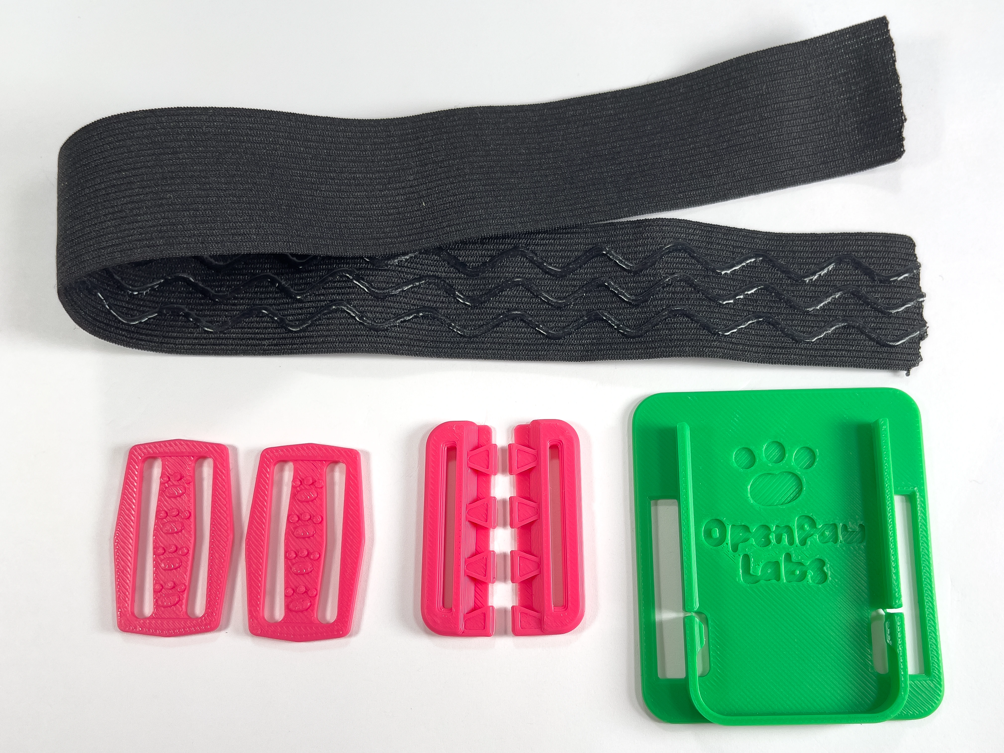
bb-lsm6dsv/diy-straps/images/strap-and-parts-img-4830.webp
