OpenPawLabs/diy-guides/bb-lsm6dsv/0-overview/images/3d-printer.webp

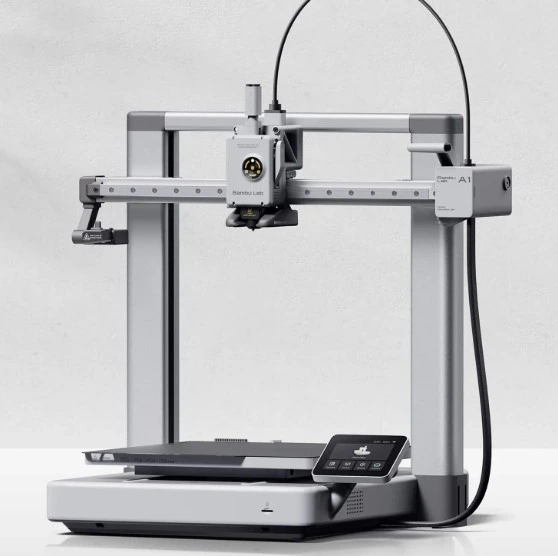
bb-lsm6dsv/0-overview/images/3d-printer.webp
