OpenPawLabs/diy-guides/bb-lsm6dsv/1-3d-prints/images/3d-printer.webp

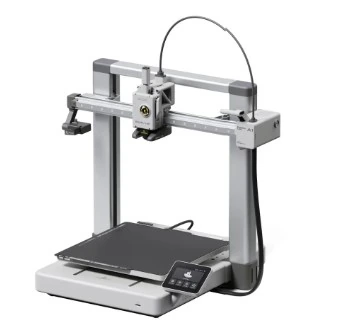
bb-lsm6dsv/1-3d-prints/images/3d-printer.webp
