OpenPawLabs/diy-guides/bb-lsm6dsv/1-3d-prints/images/3mf-print-overview-1.webp

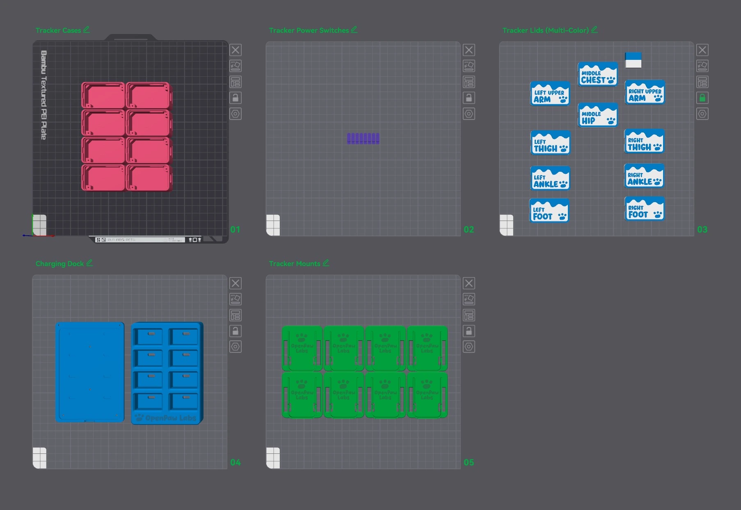
bb-lsm6dsv/1-3d-prints/images/3mf-print-overview-1.webp
