OpenPawLabs/diy-guides/bb-lsm6dsv/1-3d-prints/images/img-4574.webp

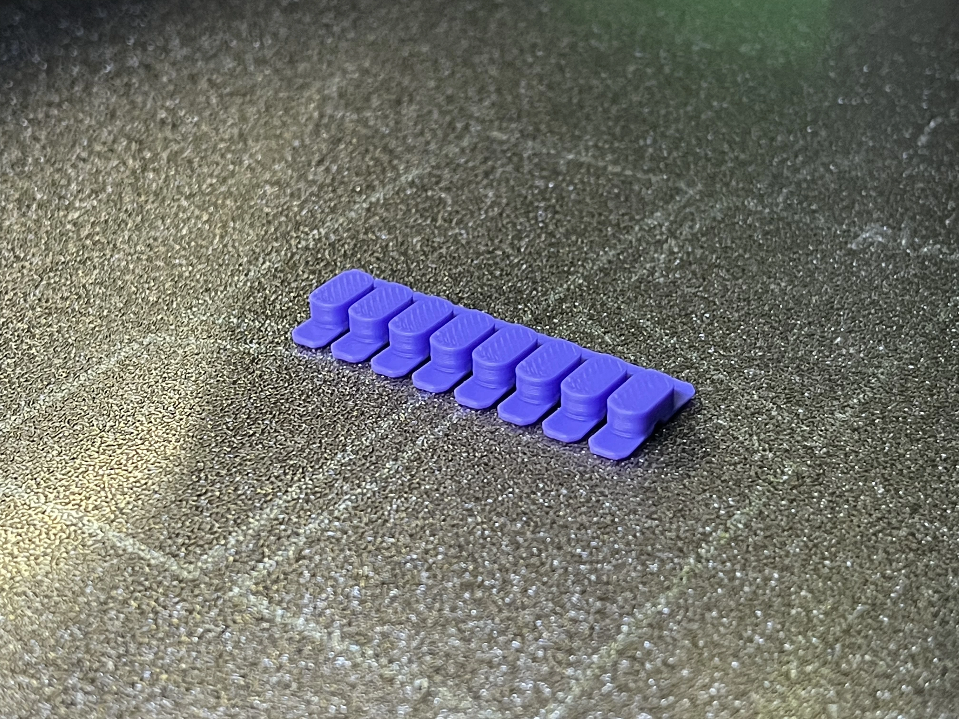
bb-lsm6dsv/1-3d-prints/images/img-4574.webp
