OpenPawLabs/diy-guides/bb-lsm6dsv/1-3d-prints/images/img-4579.webp

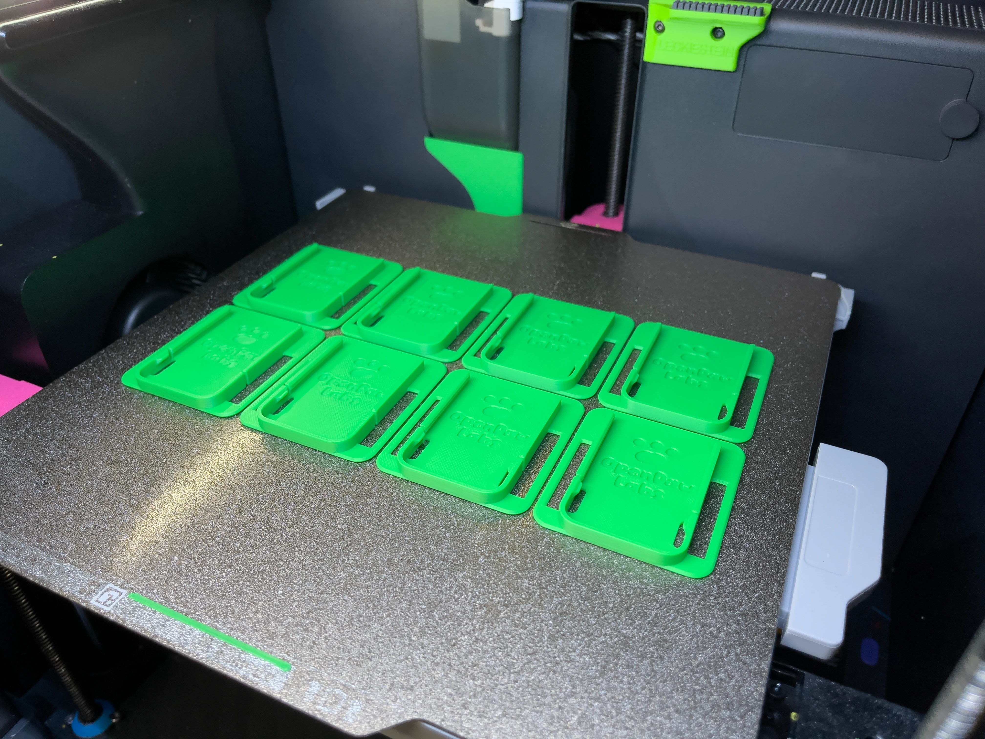
bb-lsm6dsv/1-3d-prints/images/img-4579.webp
