OpenPawLabs/diy-guides/bb-lsm6dsv/1-3d-prints/images/img-4581-1.webp

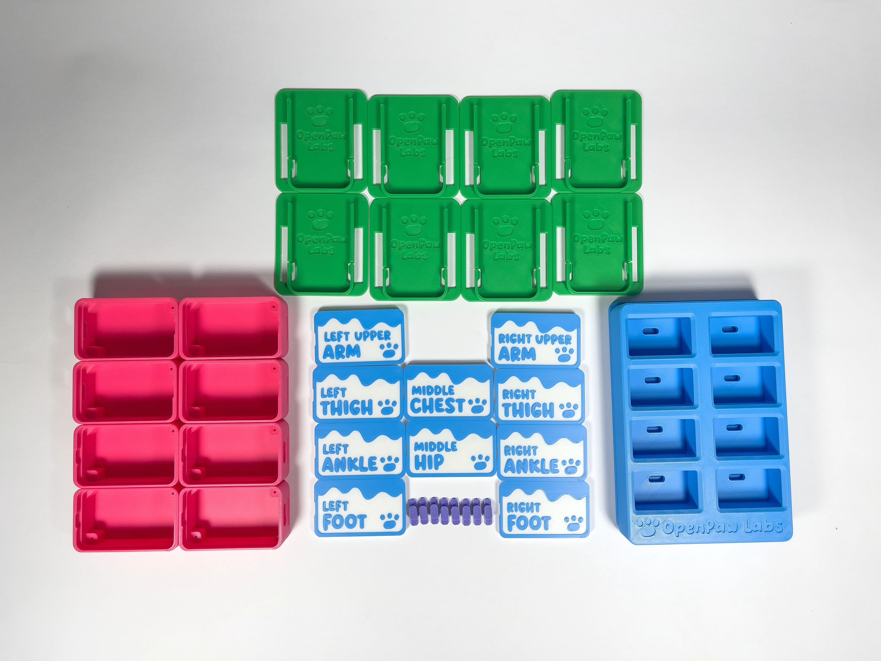
bb-lsm6dsv/1-3d-prints/images/img-4581-1.webp
