OpenPawLabs/diy-guides/bb-lsm6dsv/1-3d-prints/images/img-4718.webp

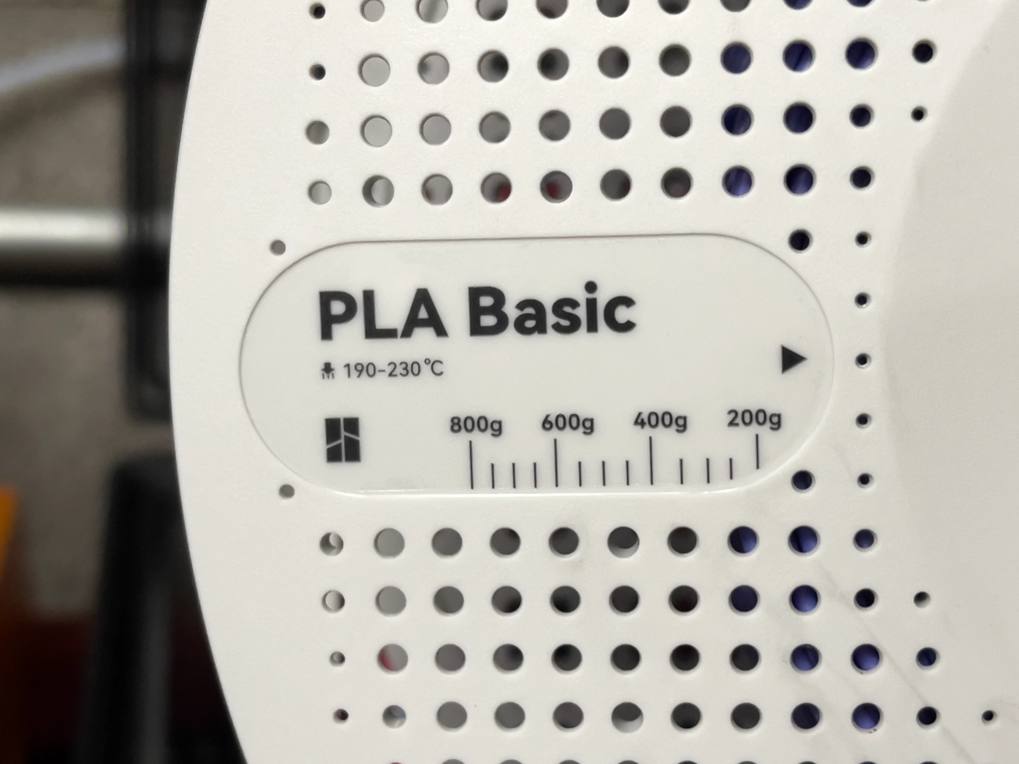
bb-lsm6dsv/1-3d-prints/images/img-4718.webp
