OpenPawLabs/diy-guides/bb-lsm6dsv/1-3d-prints/images/tracker-cases-print.webp

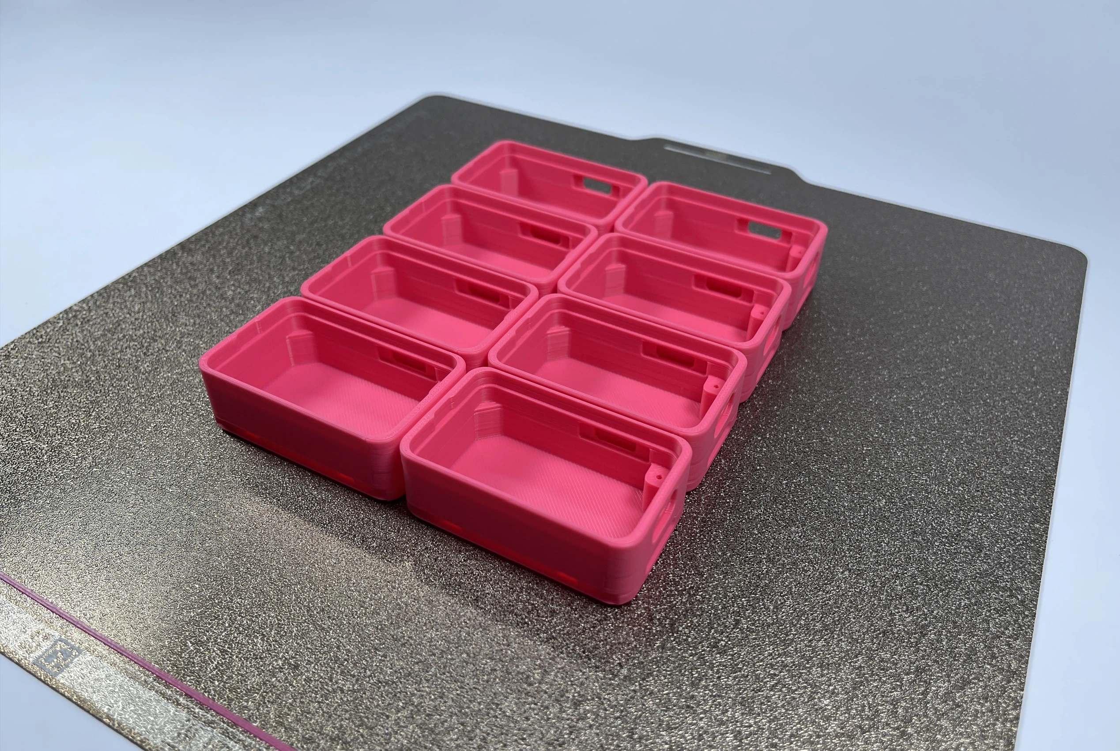
bb-lsm6dsv/1-3d-prints/images/tracker-cases-print.webp
