OpenPawLabs/diy-guides/bb-lsm6dsv/1-3d-prints/images/tracker-cases.webp

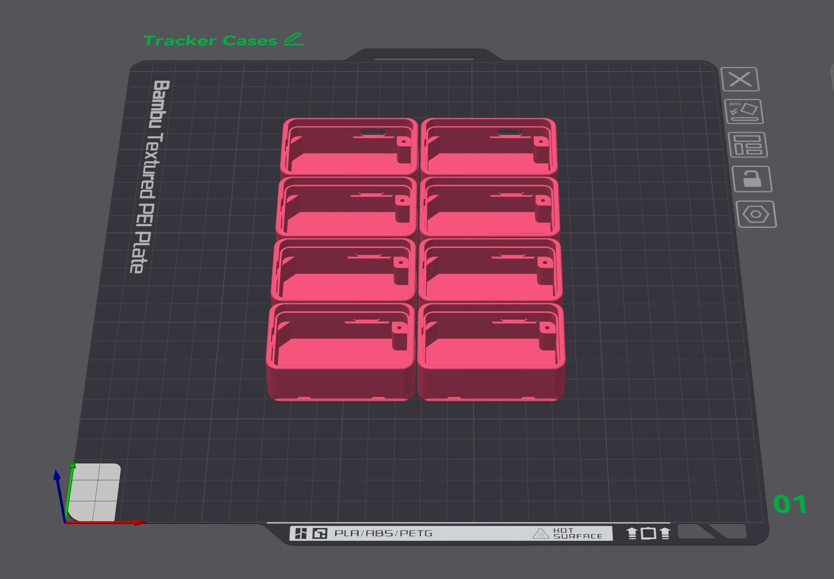
bb-lsm6dsv/1-3d-prints/images/tracker-cases.webp
