OpenPawLabs/diy-guides/bb-lsm6dsv/2-tracker-assembly/images/battery-1000mah-side-bend-transparent-cropped-img-4592-2.webp

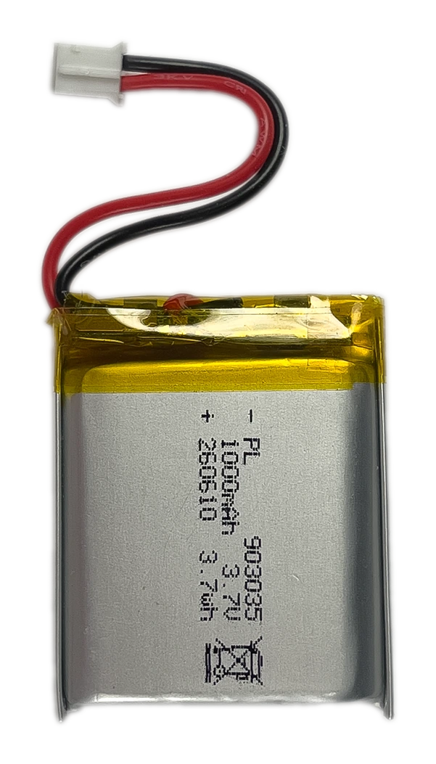
bb-lsm6dsv/2-tracker-assembly/images/battery-1000mah-side-bend-transparent-cropped-img-4592-2.webp
