OpenPawLabs/diy-guides/bb-lsm6dsv/2-tracker-assembly/images/img-4599-2-1.webp

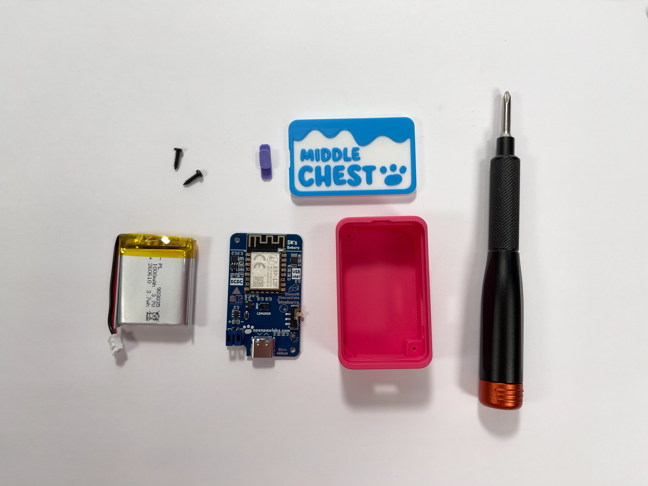
bb-lsm6dsv/2-tracker-assembly/images/img-4599-2-1.webp
