OpenPawLabs/diy-guides/bb-lsm6dsv/2-tracker-assembly/images/img-4616-2.webp

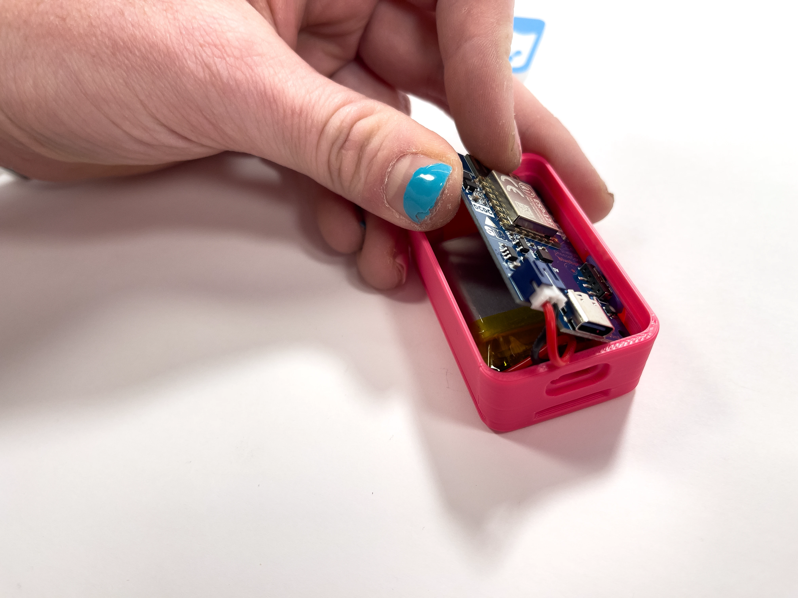
bb-lsm6dsv/2-tracker-assembly/images/img-4616-2.webp
