OpenPawLabs/diy-guides/bb-lsm6dsv/2-tracker-assembly/images/img-4618.webp

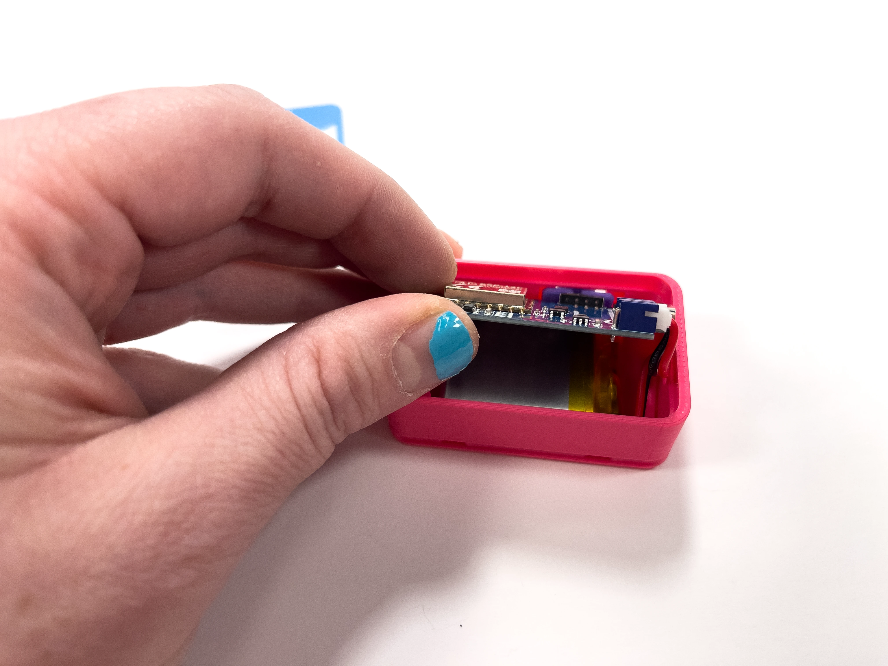
bb-lsm6dsv/2-tracker-assembly/images/img-4618.webp
