OpenPawLabs/diy-guides/bb-lsm6dsv/2-tracker-assembly/images/img-4634.webp

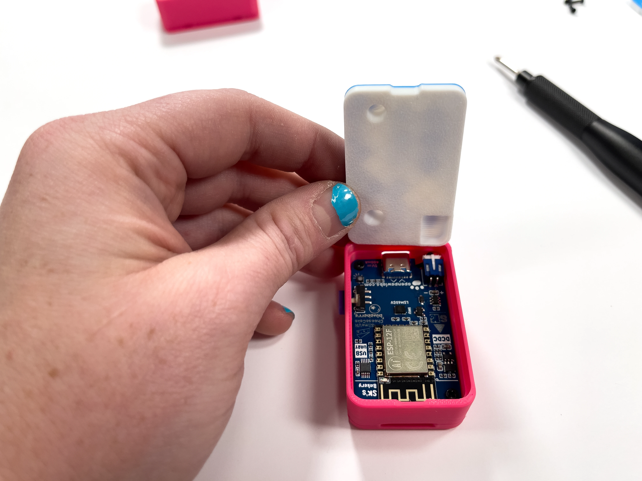
bb-lsm6dsv/2-tracker-assembly/images/img-4634.webp
