OpenPawLabs/diy-guides/bb-lsm6dsv/2-tracker-assembly/images/tracker-pcb-back-full.webp

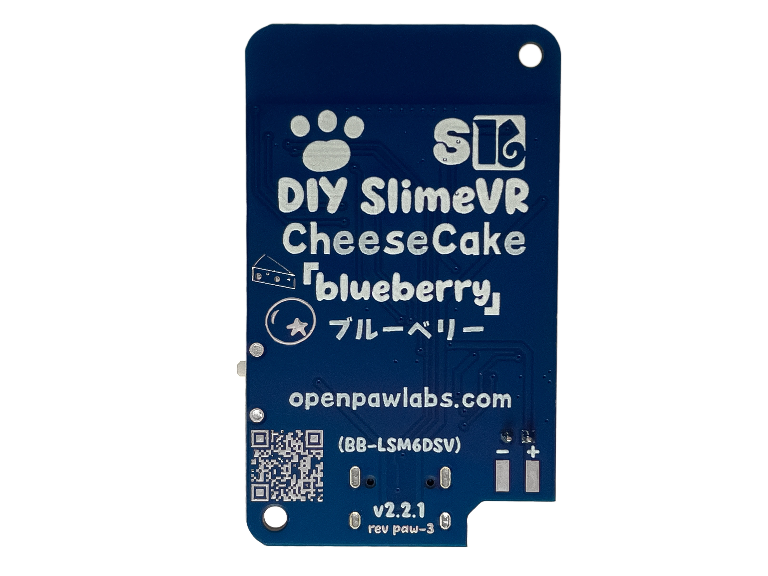
bb-lsm6dsv/2-tracker-assembly/images/tracker-pcb-back-full.webp
