OpenPawLabs/diy-guides/bb-lsm6dsv/3-dock-assembly/images/dock-w-case-transparent-img-4436.webp

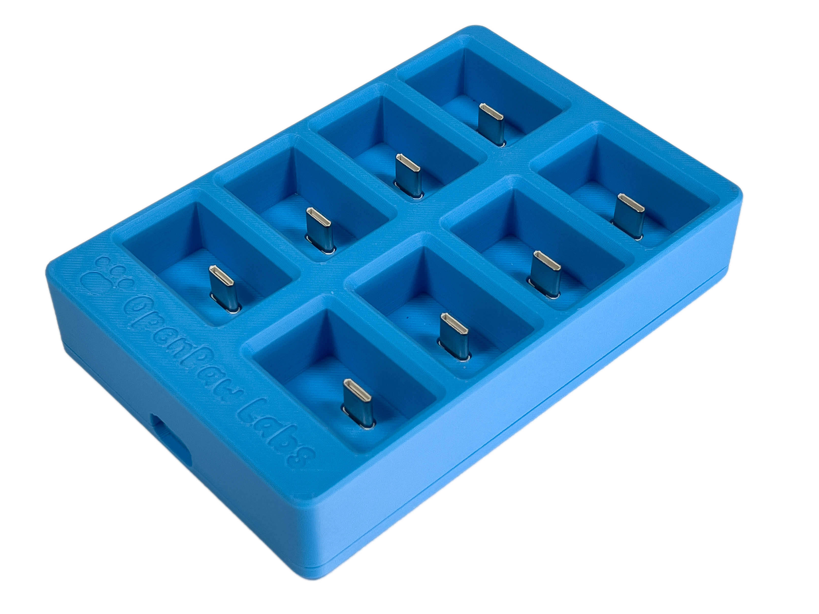
bb-lsm6dsv/3-dock-assembly/images/dock-w-case-transparent-img-4436.webp
