OpenPawLabs/diy-guides/bb-lsm6dsv/3-dock-assembly/images/img-4636-2.webp

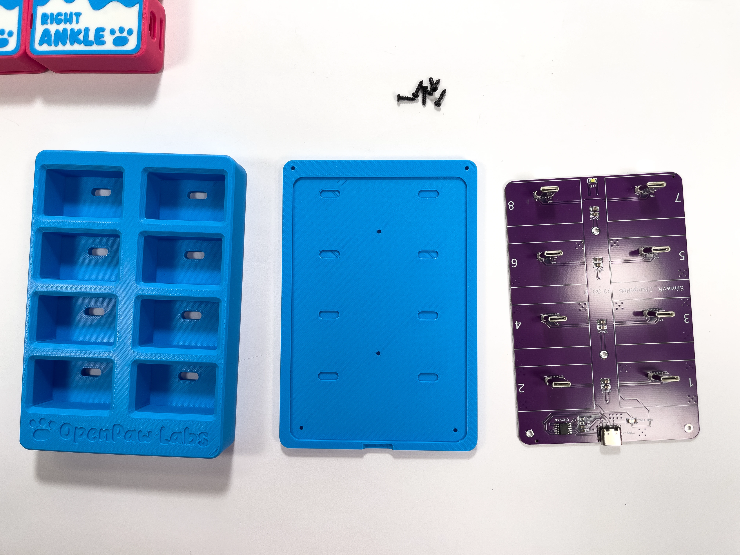
bb-lsm6dsv/3-dock-assembly/images/img-4636-2.webp
