OpenPawLabs/diy-guides/bb-lsm6dsv/3-dock-assembly/images/img-4713.webp

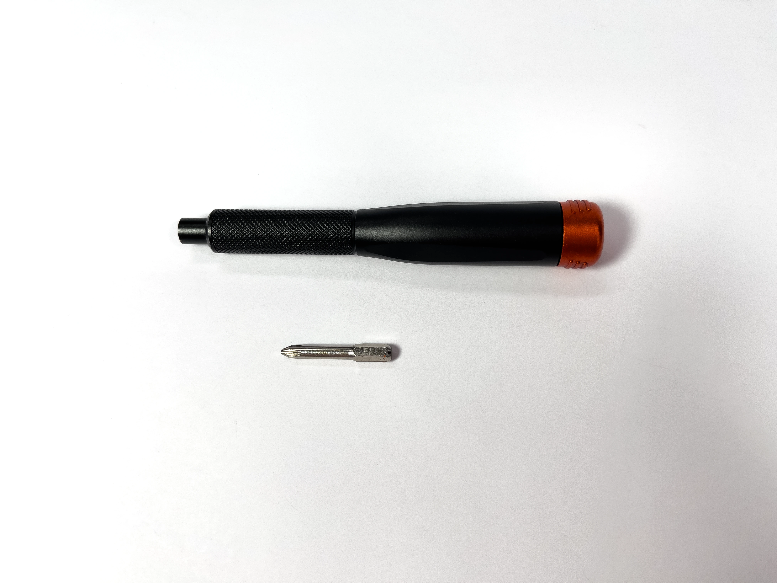
bb-lsm6dsv/3-dock-assembly/images/img-4713.webp
