OpenPawLabs/diy-guides/bb-lsm6dsv/3-dock-assembly/images/trackers-transparent-img-4525.webp

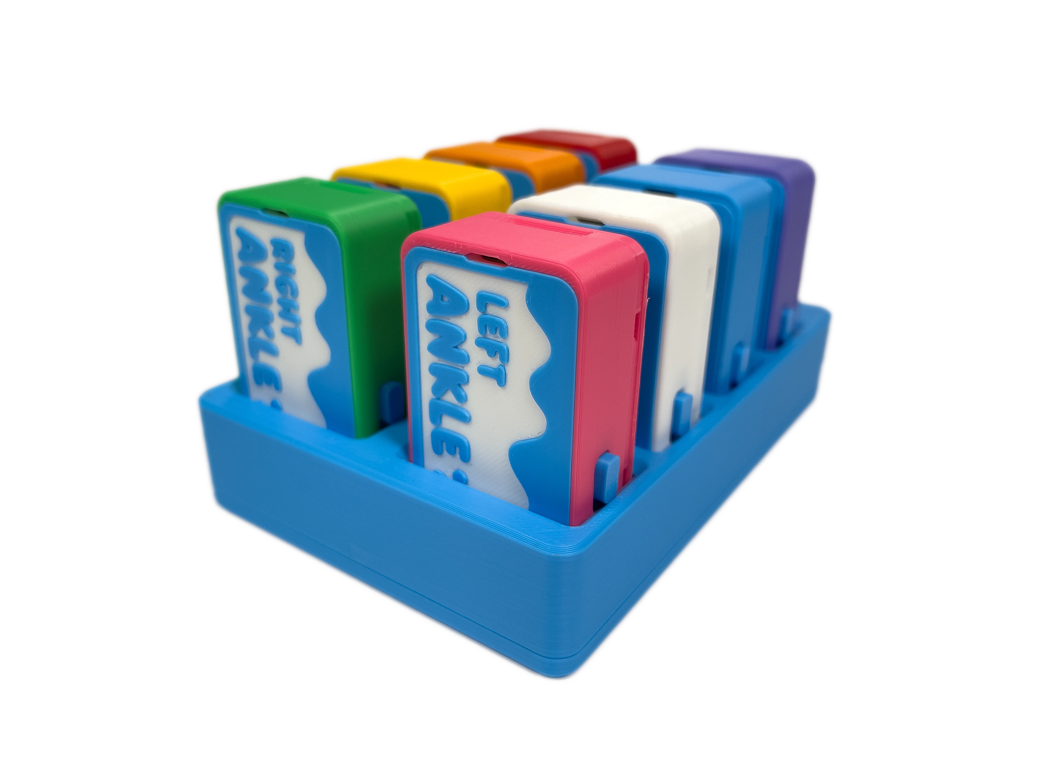
bb-lsm6dsv/3-dock-assembly/images/trackers-transparent-img-4525.webp
