OpenPawLabs/diy-guides/bb-lsm6dsv/4-strap-assembly/images/img-4644.webp

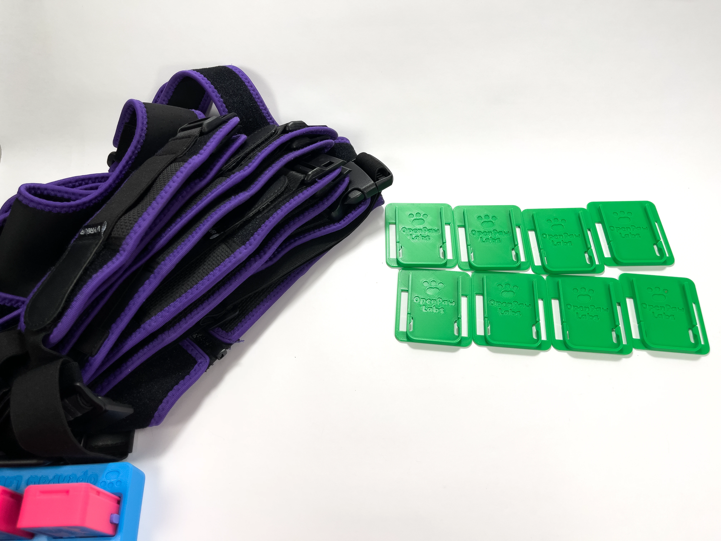
bb-lsm6dsv/4-strap-assembly/images/img-4644.webp
