OpenPawLabs/diy-guides/bb-lsm6dsv/4-strap-assembly/images/img-4645.webp

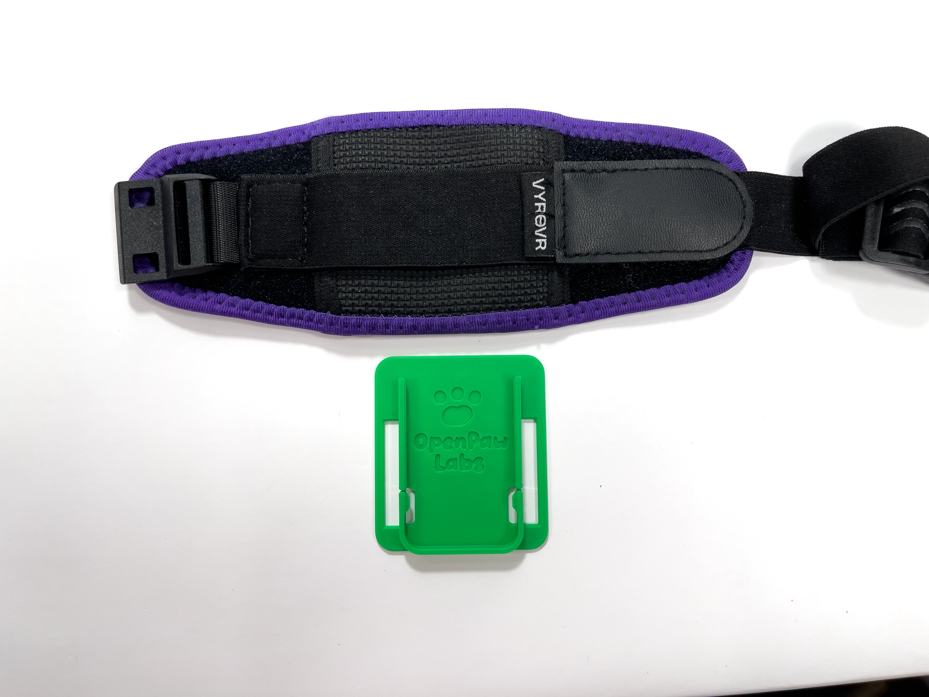
bb-lsm6dsv/4-strap-assembly/images/img-4645.webp
