OpenPawLabs/diy-guides/bb-lsm6dsv/4-strap-assembly/images/img-4650.webp

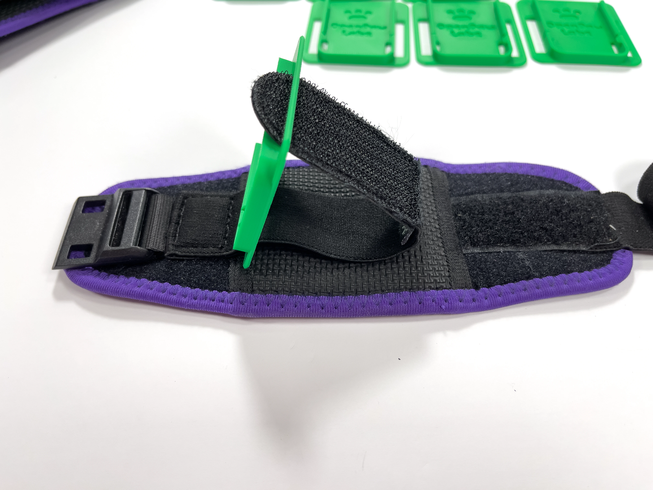
bb-lsm6dsv/4-strap-assembly/images/img-4650.webp
