OpenPawLabs/diy-guides/bb-lsm6dsv/4-strap-assembly/images/img-4653.webp

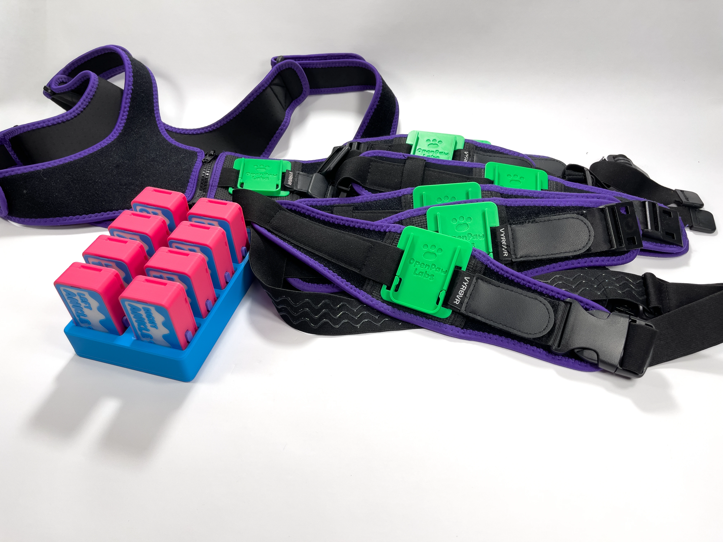
bb-lsm6dsv/4-strap-assembly/images/img-4653.webp
