OpenPawLabs/diy-guides/bb-lsm6dsv/4-strap-assembly/images/img-4656-2.webp

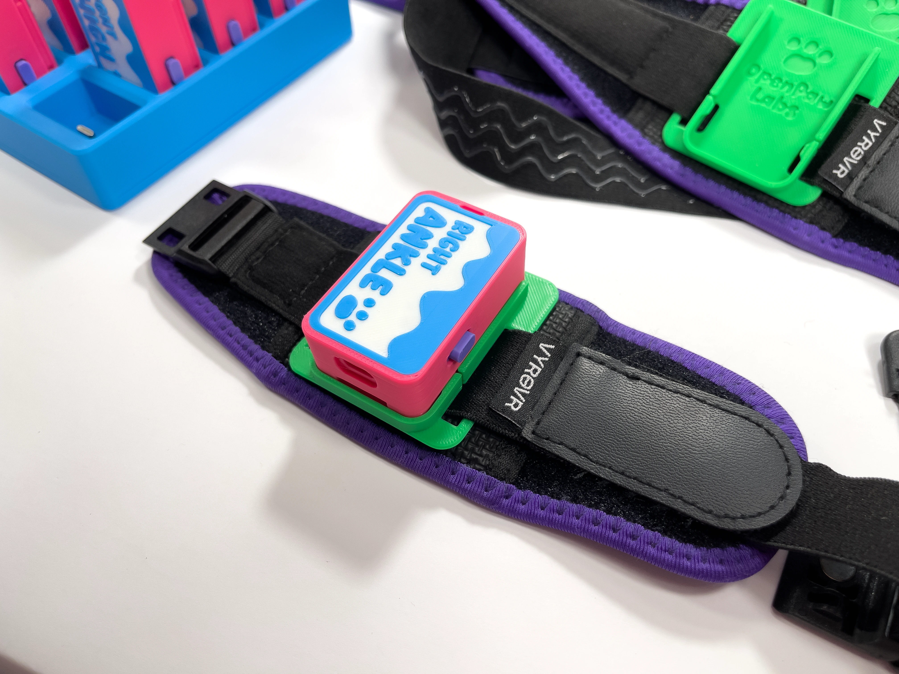
bb-lsm6dsv/4-strap-assembly/images/img-4656-2.webp
