OpenPawLabs/diy-guides/common/0-onetime-tracker-setup/images/slimevr-all-trackers-connected-confirm.webp

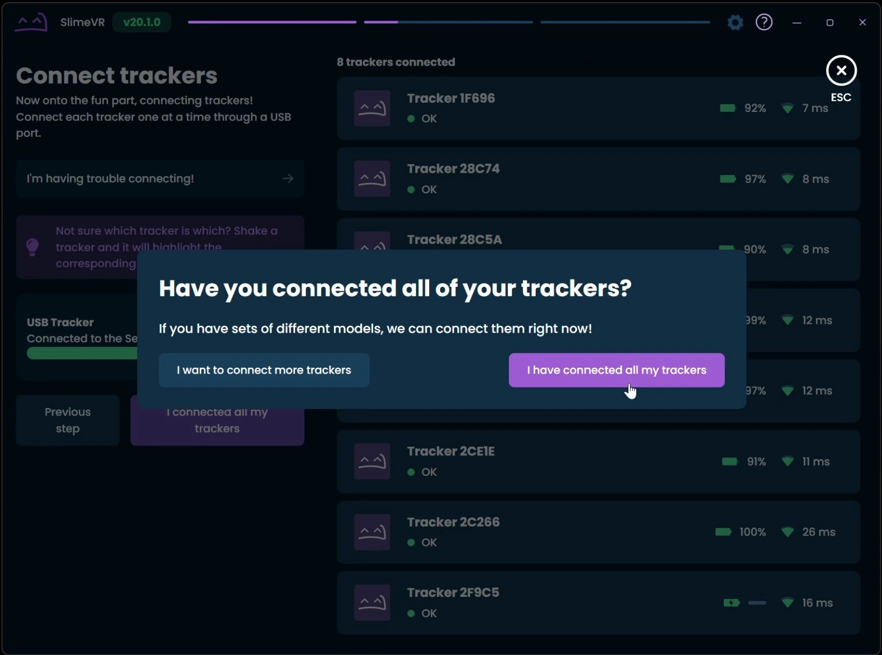
common/0-onetime-tracker-setup/images/slimevr-all-trackers-connected-confirm.webp
