OpenPawLabs/diy-guides/common/0-onetime-tracker-setup/images/slimevr-assign-tracker-body-part.webp

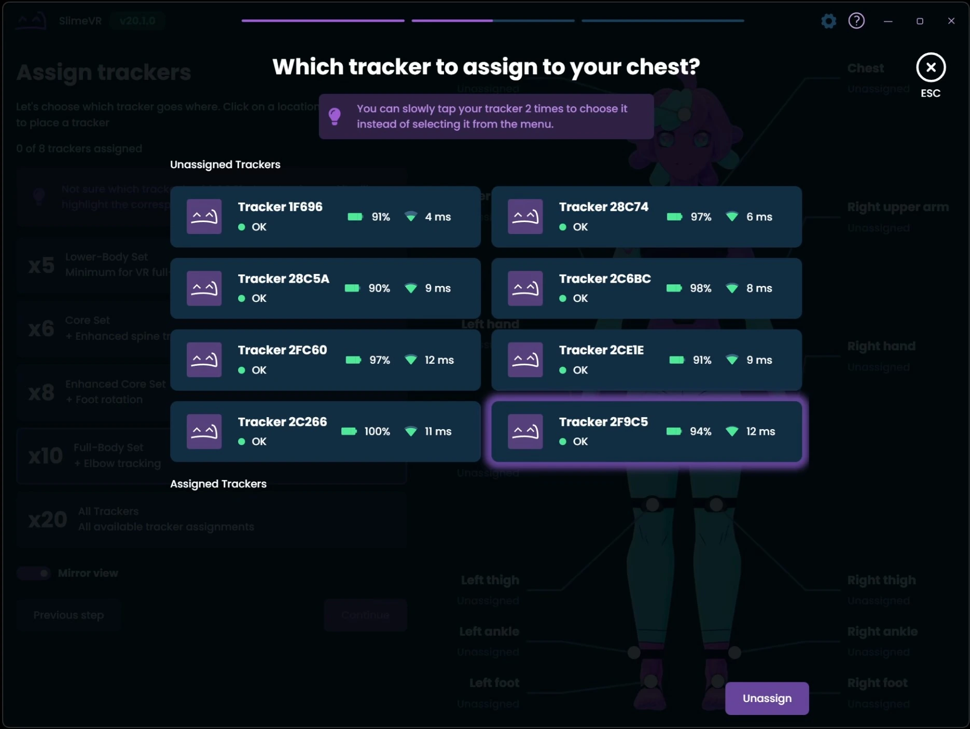
common/0-onetime-tracker-setup/images/slimevr-assign-tracker-body-part.webp
