OpenPawLabs/diy-guides/common/0-onetime-tracker-setup/images/slimevr-auto-mounting-select.webp

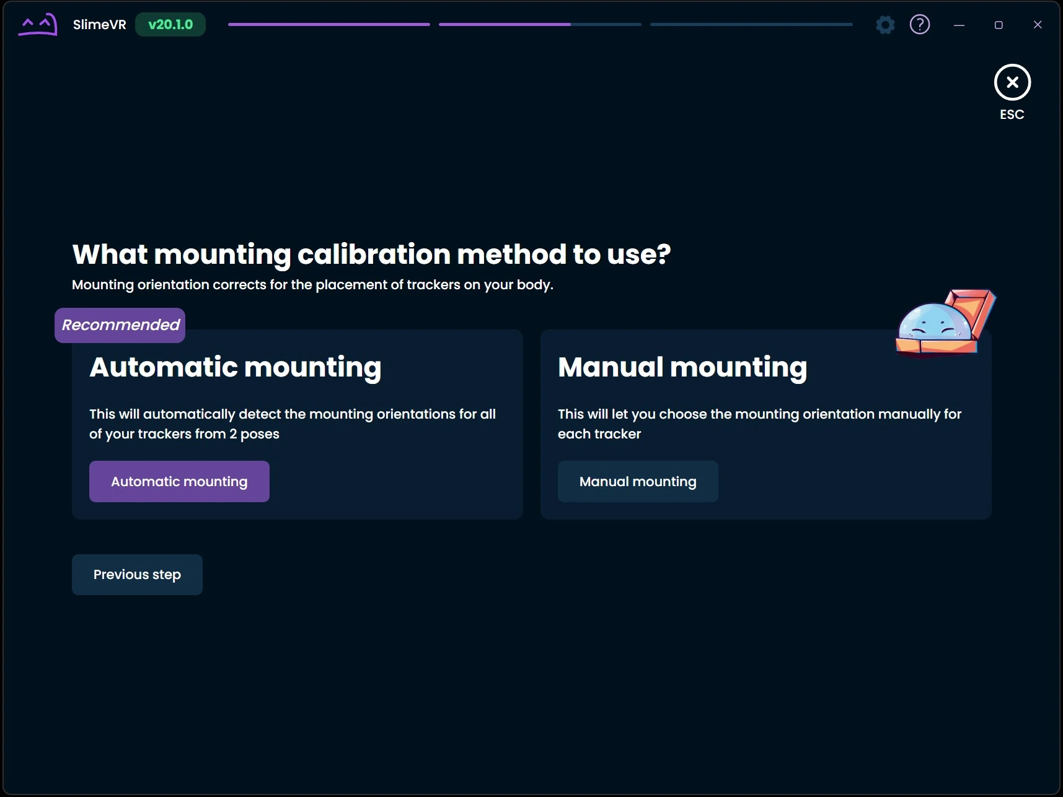
common/0-onetime-tracker-setup/images/slimevr-auto-mounting-select.webp
