OpenPawLabs/diy-guides/common/0-onetime-tracker-setup/images/slimevr-connect-trackers.webp

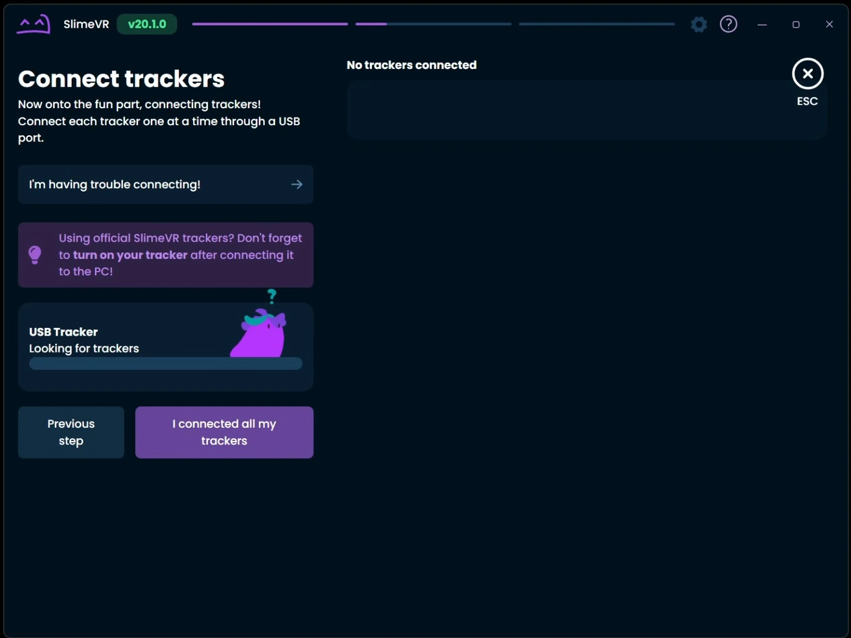
common/0-onetime-tracker-setup/images/slimevr-connect-trackers.webp
