OpenPawLabs/diy-guides/common/0-onetime-tracker-setup/images/slimevr-download.webp

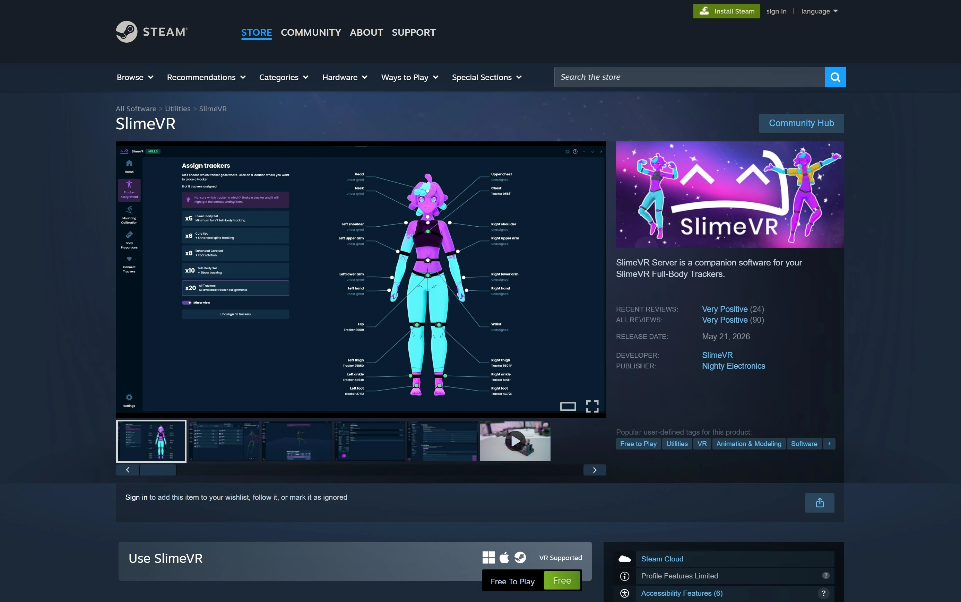
common/0-onetime-tracker-setup/images/slimevr-download.webp
