OpenPawLabs/diy-guides/common/0-onetime-tracker-setup/images/slimevr-go-to-vrchat-warnings.webp

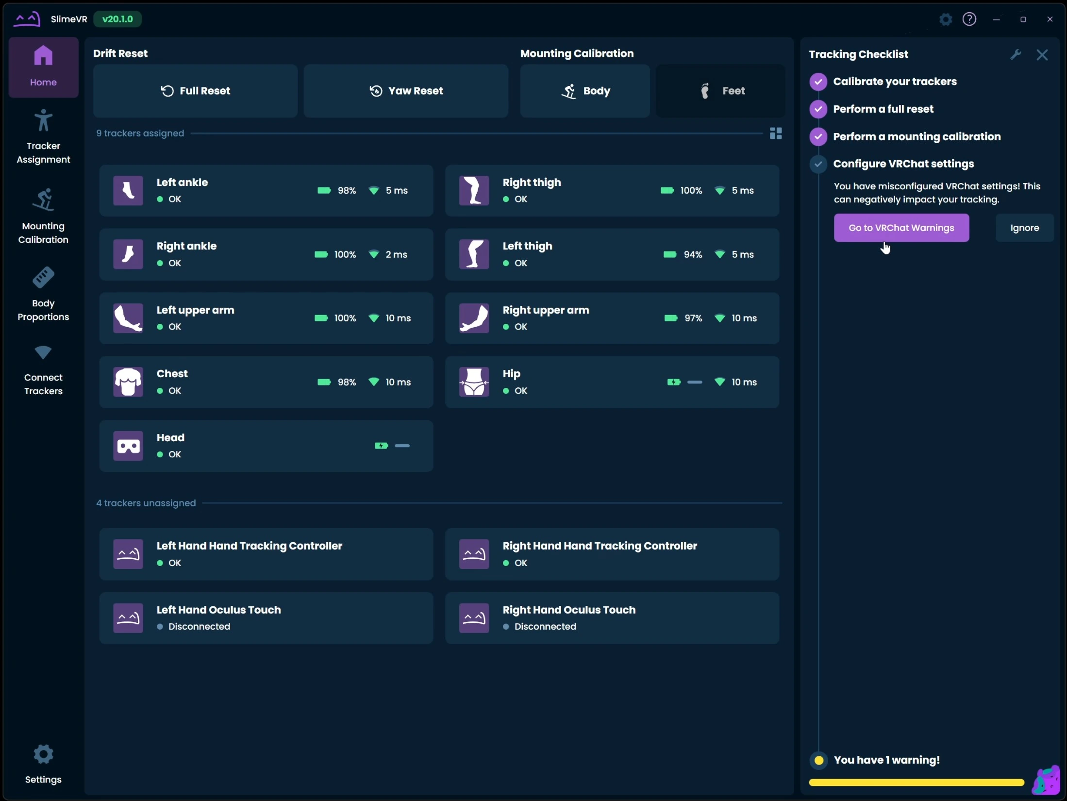
common/0-onetime-tracker-setup/images/slimevr-go-to-vrchat-warnings.webp
