OpenPawLabs/diy-guides/common/0-onetime-tracker-setup/images/slimevr-height-setup.webp

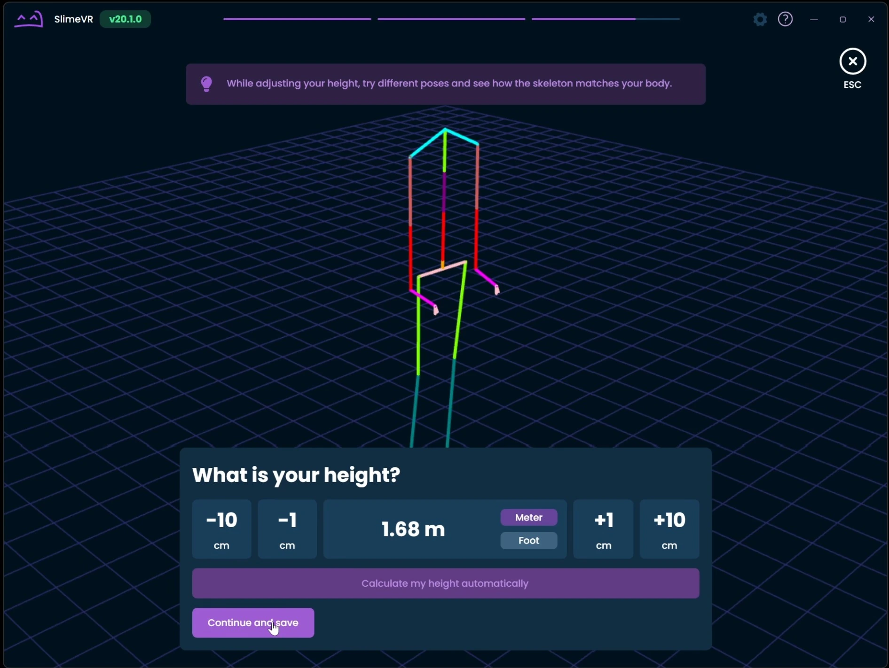
common/0-onetime-tracker-setup/images/slimevr-height-setup.webp
