OpenPawLabs/diy-guides/common/0-onetime-tracker-setup/images/slimevr-install-mark-private.webp

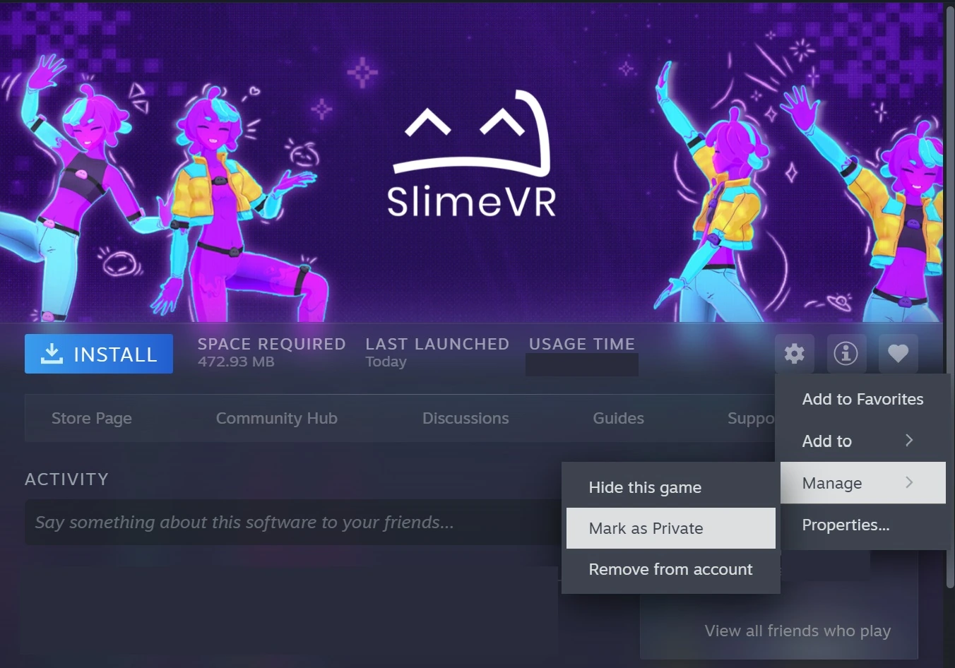
common/0-onetime-tracker-setup/images/slimevr-install-mark-private.webp
