OpenPawLabs/diy-guides/common/0-onetime-tracker-setup/images/slimevr-lets-get-started-1.webp

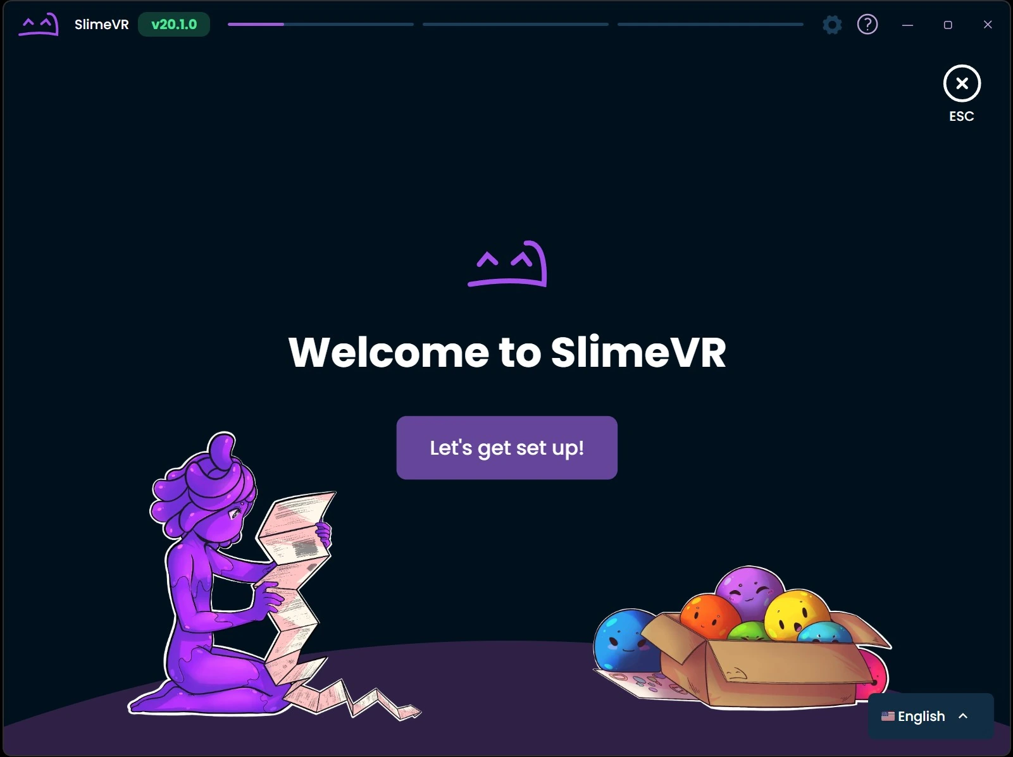
common/0-onetime-tracker-setup/images/slimevr-lets-get-started-1.webp
