OpenPawLabs/diy-guides/common/0-onetime-tracker-setup/images/slimevr-no-trackers-detected.webp

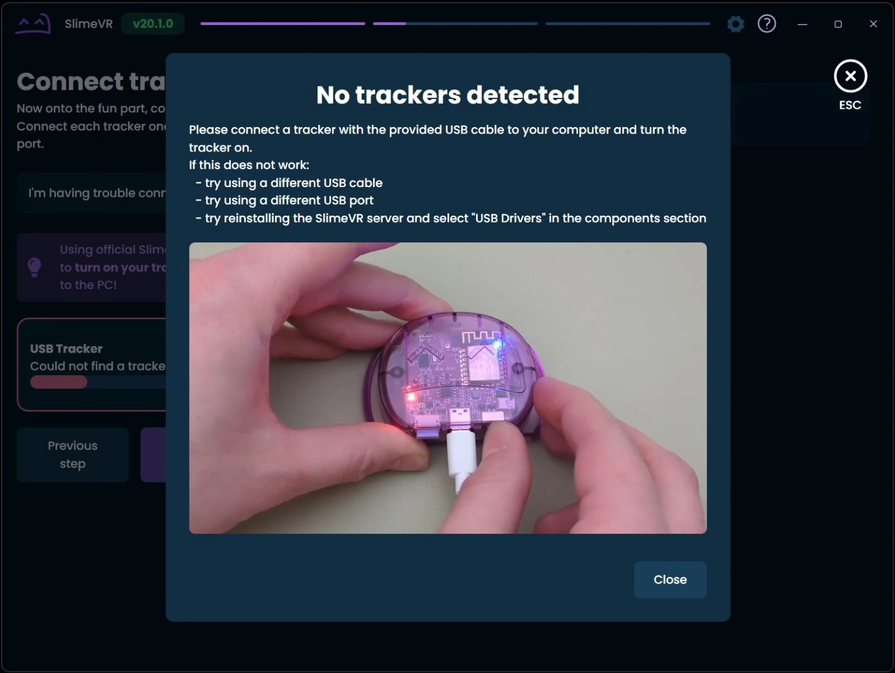
common/0-onetime-tracker-setup/images/slimevr-no-trackers-detected.webp
