OpenPawLabs/diy-guides/common/0-onetime-tracker-setup/images/slimevr-open-stay-aligned.webp

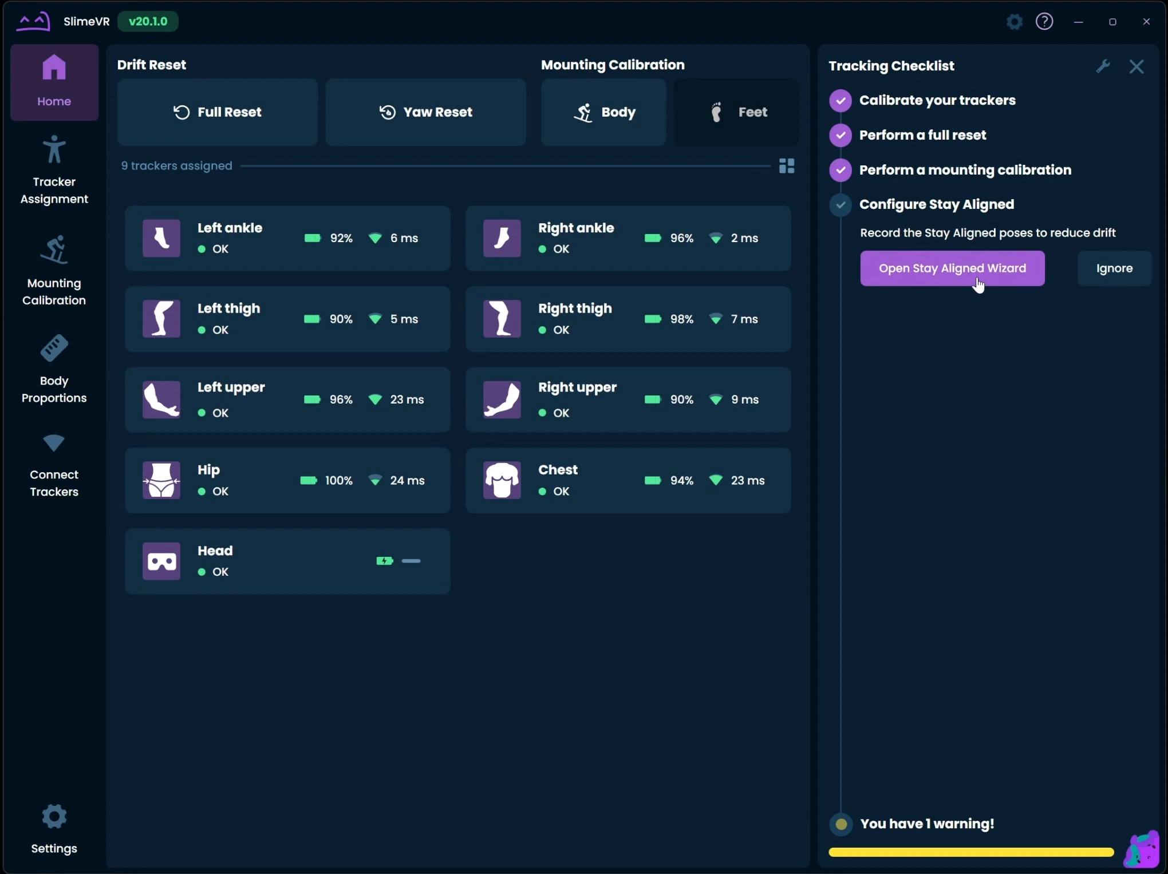
common/0-onetime-tracker-setup/images/slimevr-open-stay-aligned.webp
