OpenPawLabs/diy-guides/common/0-onetime-tracker-setup/images/slimevr-select-tracker-type.webp

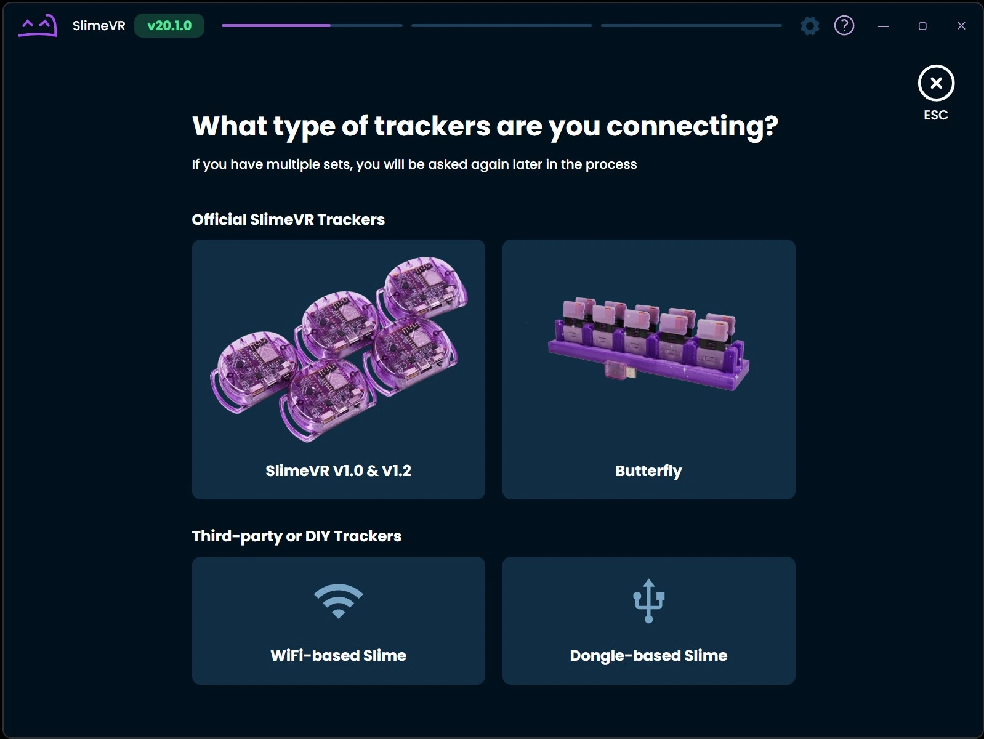
common/0-onetime-tracker-setup/images/slimevr-select-tracker-type.webp
