OpenPawLabs/diy-guides/common/0-onetime-tracker-setup/images/slimevr-steamvr-standalone.webp

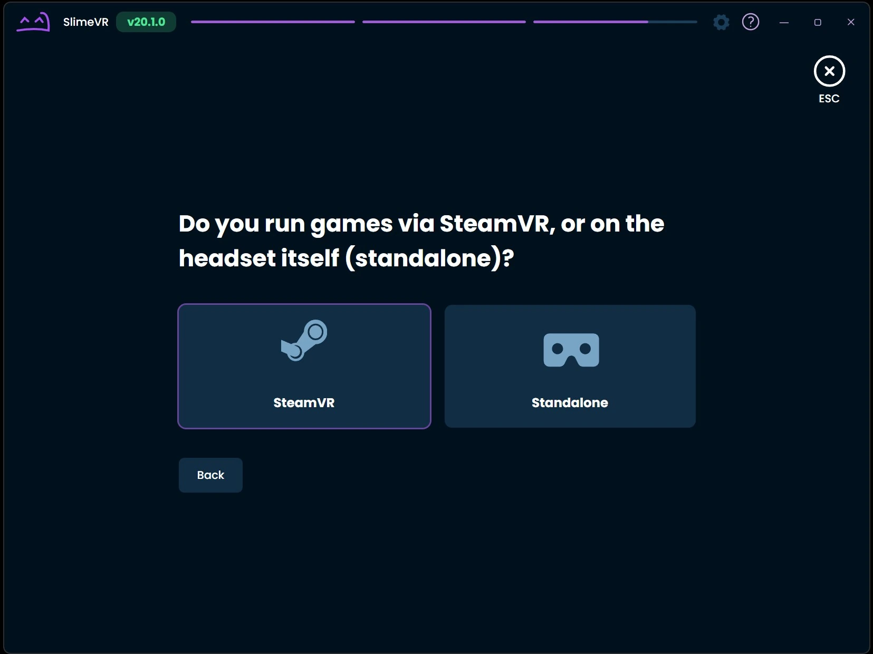
common/0-onetime-tracker-setup/images/slimevr-steamvr-standalone.webp
