OpenPawLabs/diy-guides/common/0-onetime-tracker-setup/images/slimevr-use-type-1.webp

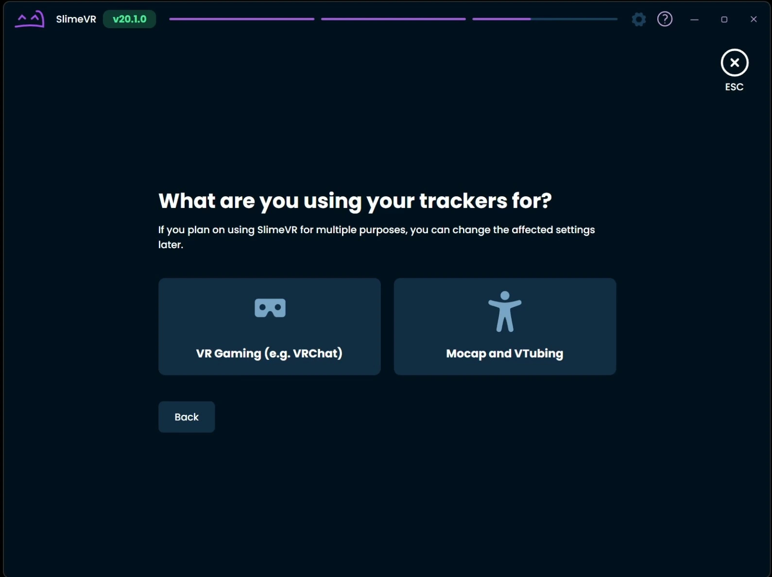
common/0-onetime-tracker-setup/images/slimevr-use-type-1.webp
