OpenPawLabs/diy-guides/common/0-onetime-tracker-setup/images/slimevr-vrchat-bigmenu-warnings.webp

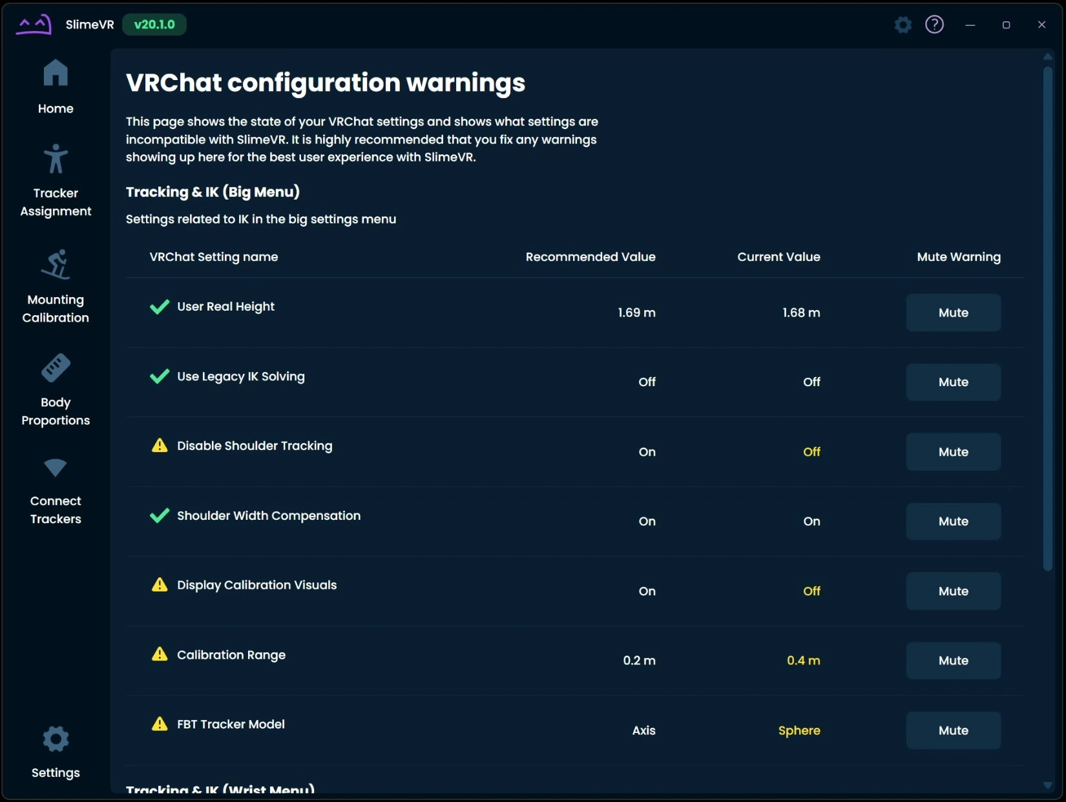
common/0-onetime-tracker-setup/images/slimevr-vrchat-bigmenu-warnings.webp
