OpenPawLabs/diy-guides/common/0-onetime-tracker-setup/images/slimevr-vrchat-wrist-menu-warnings.webp

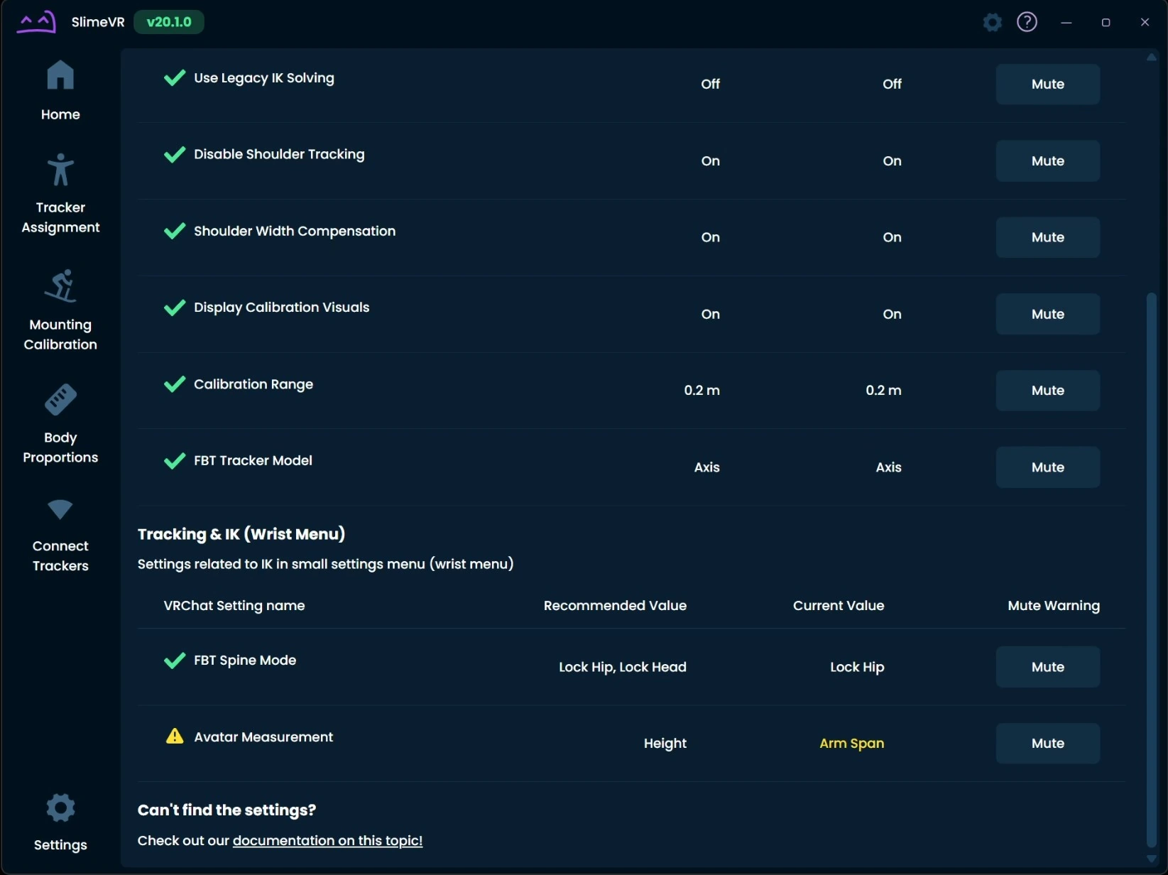
common/0-onetime-tracker-setup/images/slimevr-vrchat-wrist-menu-warnings.webp
