OpenPawLabs/diy-guides/common/0-onetime-tracker-setup/images/slimevr-wifi-connected.webp

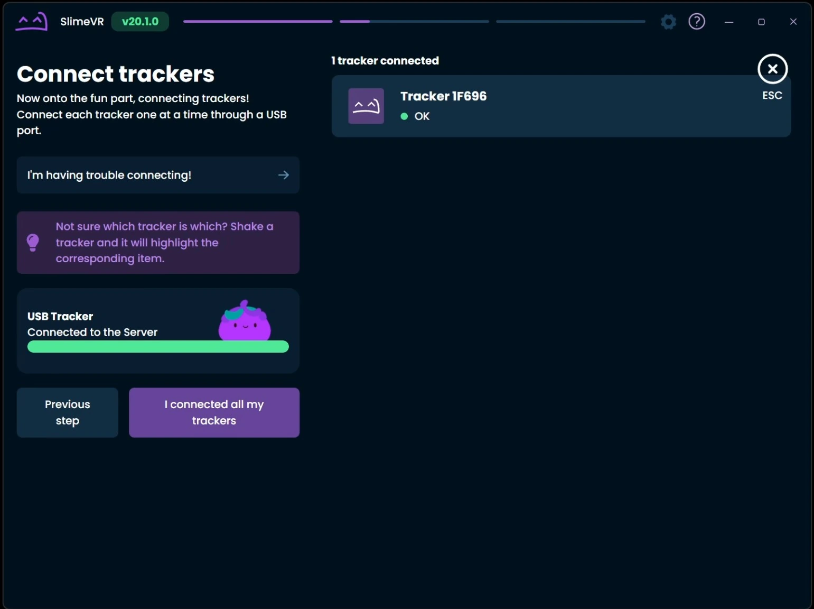
common/0-onetime-tracker-setup/images/slimevr-wifi-connected.webp
