OpenPawLabs/diy-guides/common/0-onetime-tracker-setup/images/slimevr-wifi-input-2.webp

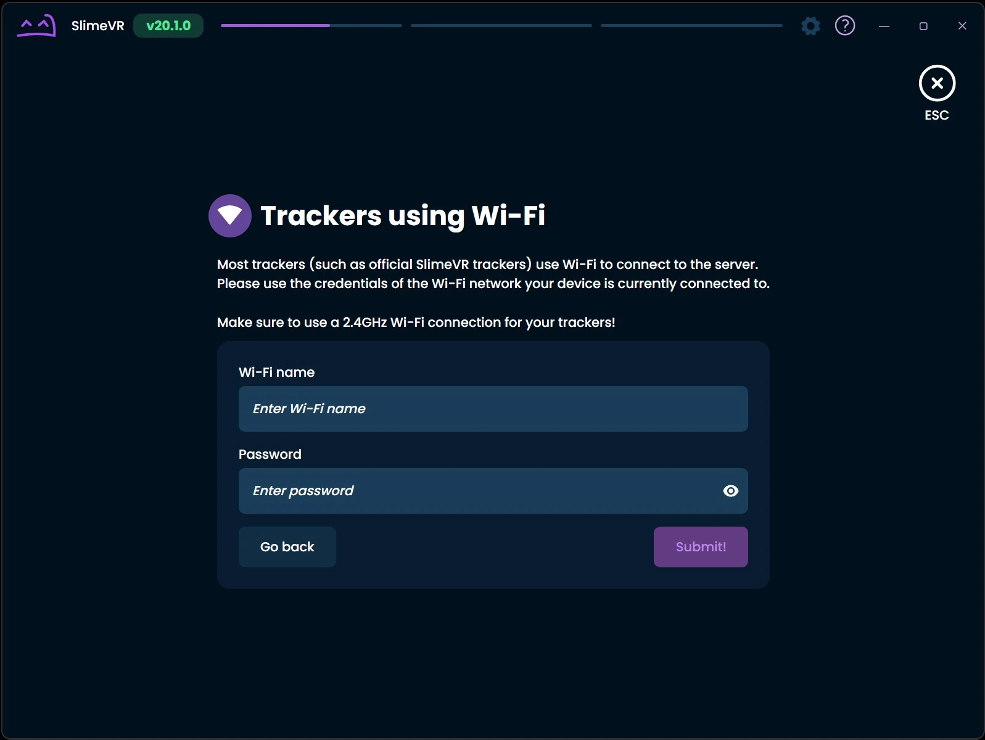
common/0-onetime-tracker-setup/images/slimevr-wifi-input-2.webp
