OpenPawLabs/diy-guides/common/0-onetime-tracker-setup/images/slimevr-window.webp

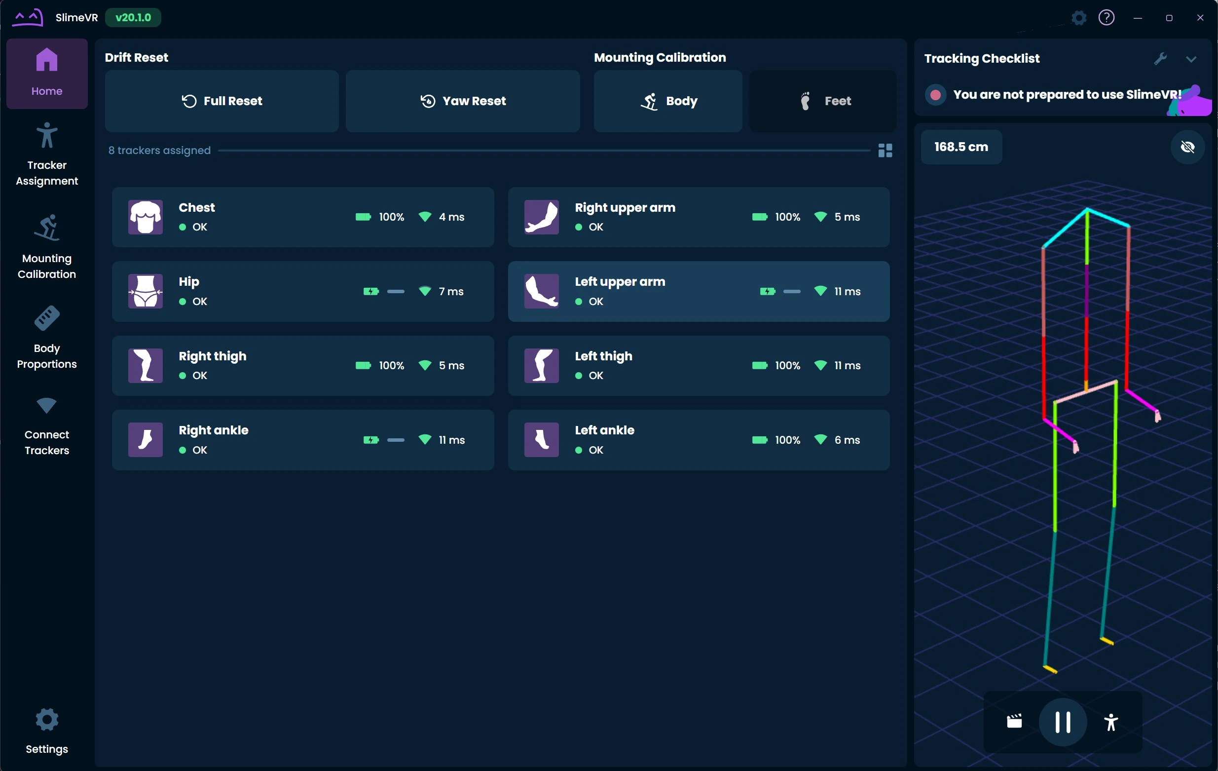
common/0-onetime-tracker-setup/images/slimevr-window.webp
