OpenPawLabs/diy-guides/common/0-onetime-tracker-setup/images/stay-aligned-pose-3.webp

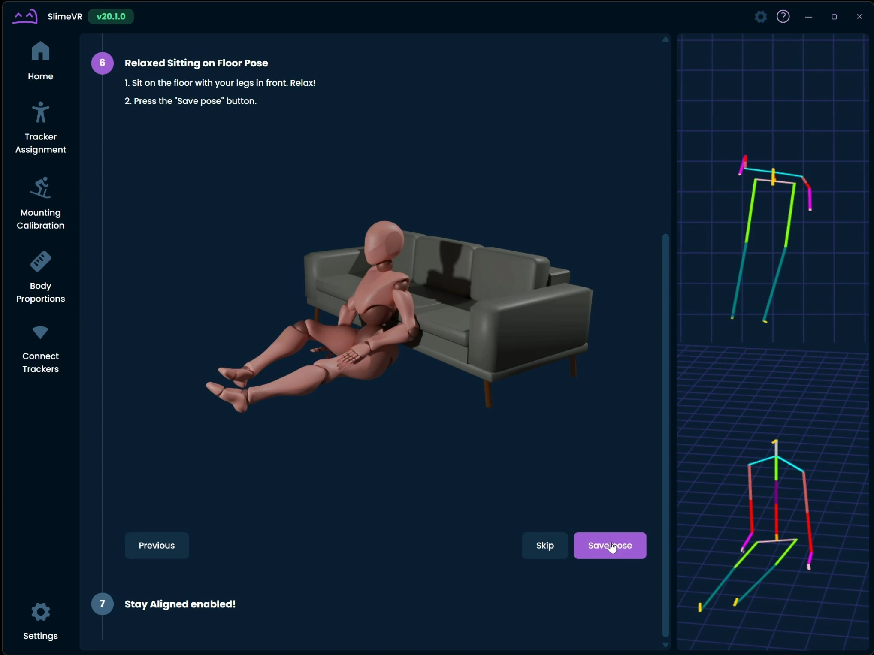
common/0-onetime-tracker-setup/images/stay-aligned-pose-3.webp
