OpenPawLabs/diy-guides/common/0-onetime-tracker-setup/images/tracker-plugged-in.webp

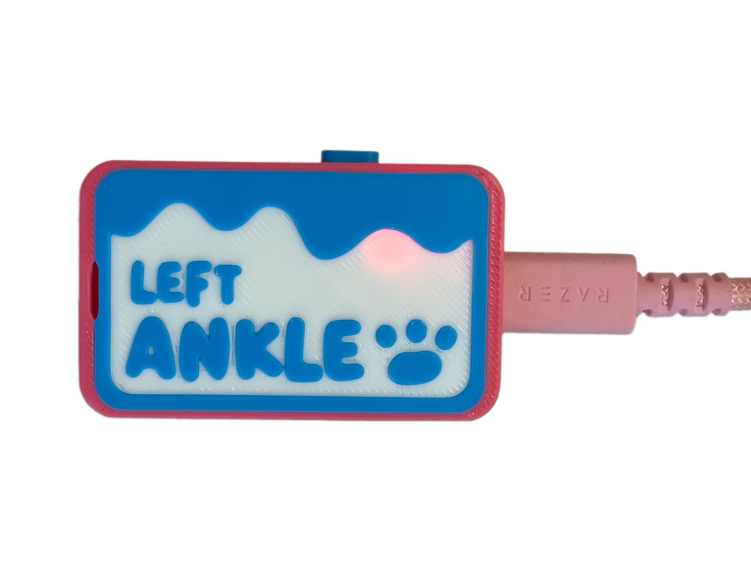
common/0-onetime-tracker-setup/images/tracker-plugged-in.webp
