OpenPawLabs/diy-guides/common/0-onetime-tracker-setup/images/vrchat-bigmenu-1.webp

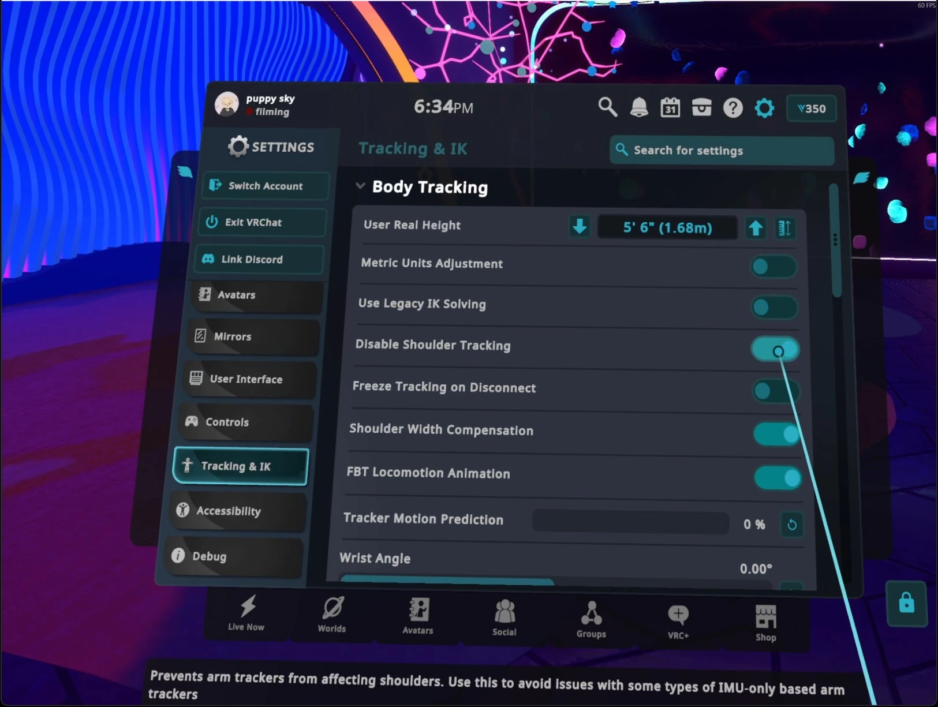
common/0-onetime-tracker-setup/images/vrchat-bigmenu-1.webp
