OpenPawLabs/diy-guides/common/0-onetime-tracker-setup/images/vrchat-bigmenu-2.webp

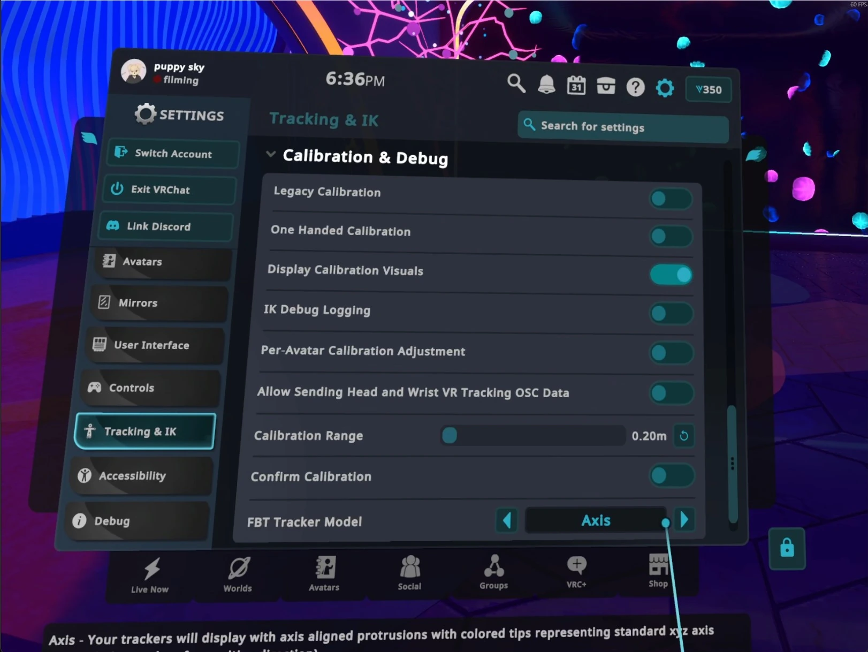
common/0-onetime-tracker-setup/images/vrchat-bigmenu-2.webp
