OpenPawLabs/diy-guides/common/0-onetime-tracker-setup/images/vrchat-wrist-menu-1.webp

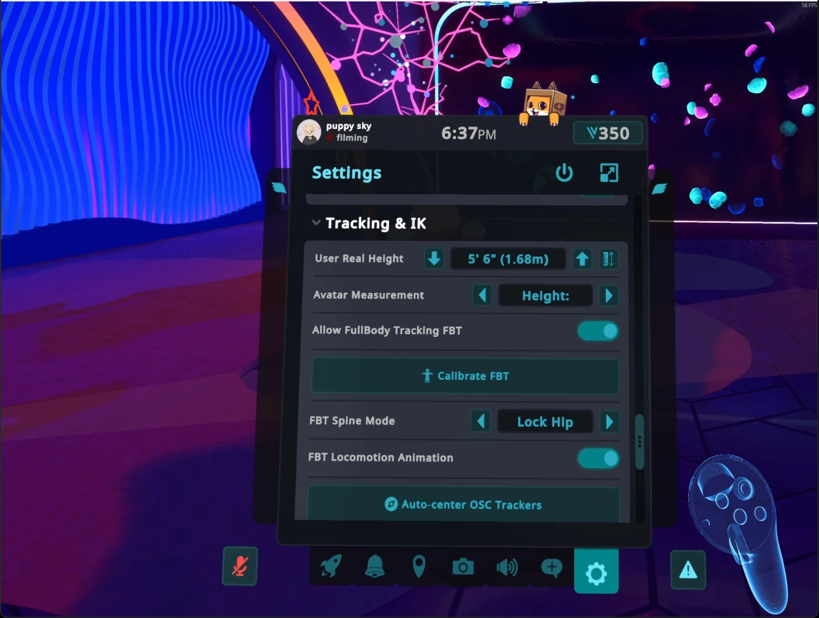
common/0-onetime-tracker-setup/images/vrchat-wrist-menu-1.webp
