OpenPawLabs/diy-guides/common/0-onetime-tracker-setup/images/slimevr-mounting-calibration-ski-pose.webp

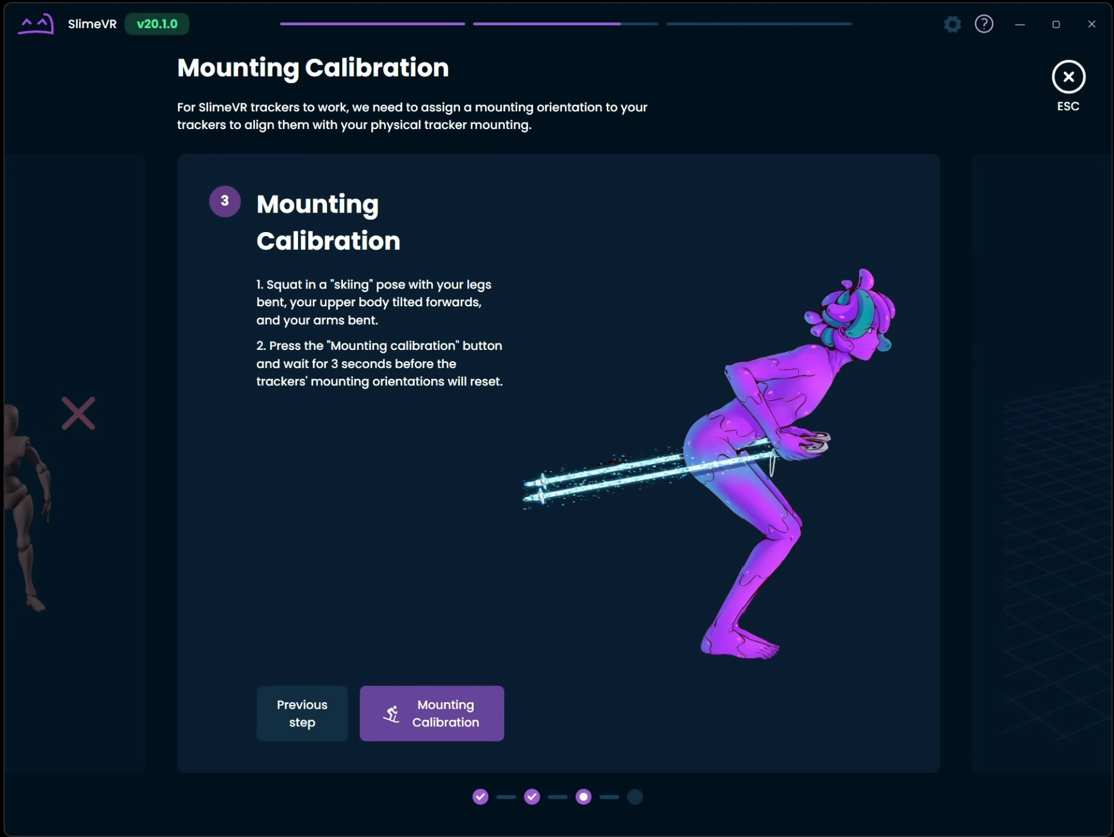
common/0-onetime-tracker-setup/images/slimevr-mounting-calibration-ski-pose.webp
