OpenPawLabs/diy-guides/common/0-onetime-tracker-setup/images/vrchat-calibration-complete.webp

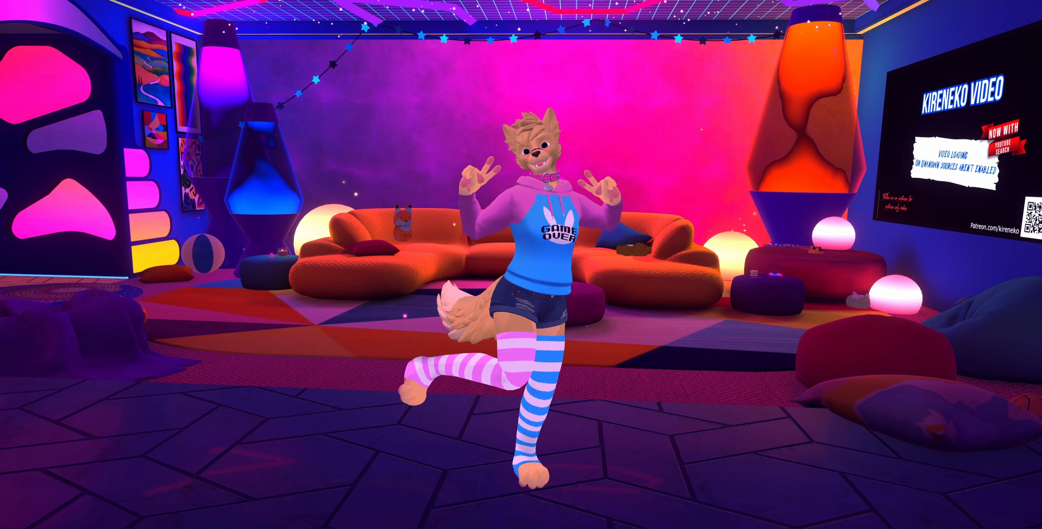
common/0-onetime-tracker-setup/images/vrchat-calibration-complete.webp
