OpenPawLabs/diy-guides/common/0-onetime-tracker-setup/images/vrchat-radial-menu-calibration-mirror.webp

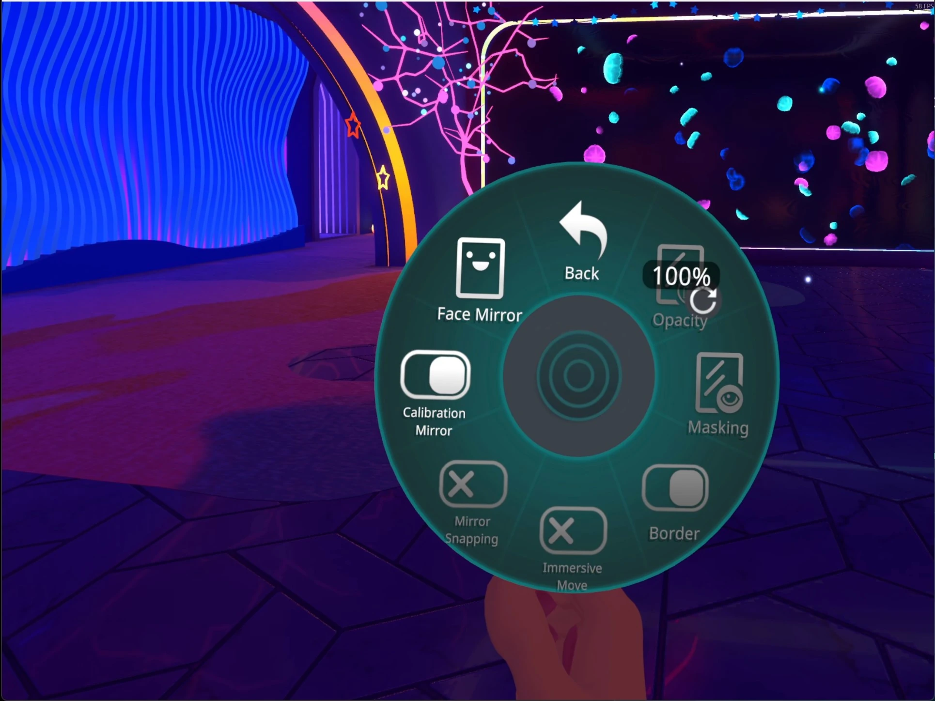
common/0-onetime-tracker-setup/images/vrchat-radial-menu-calibration-mirror.webp
