OpenPawLabs/diy-guides/common/1-vrchat-use/images/slimevr-calibrate-your-trackers.webp

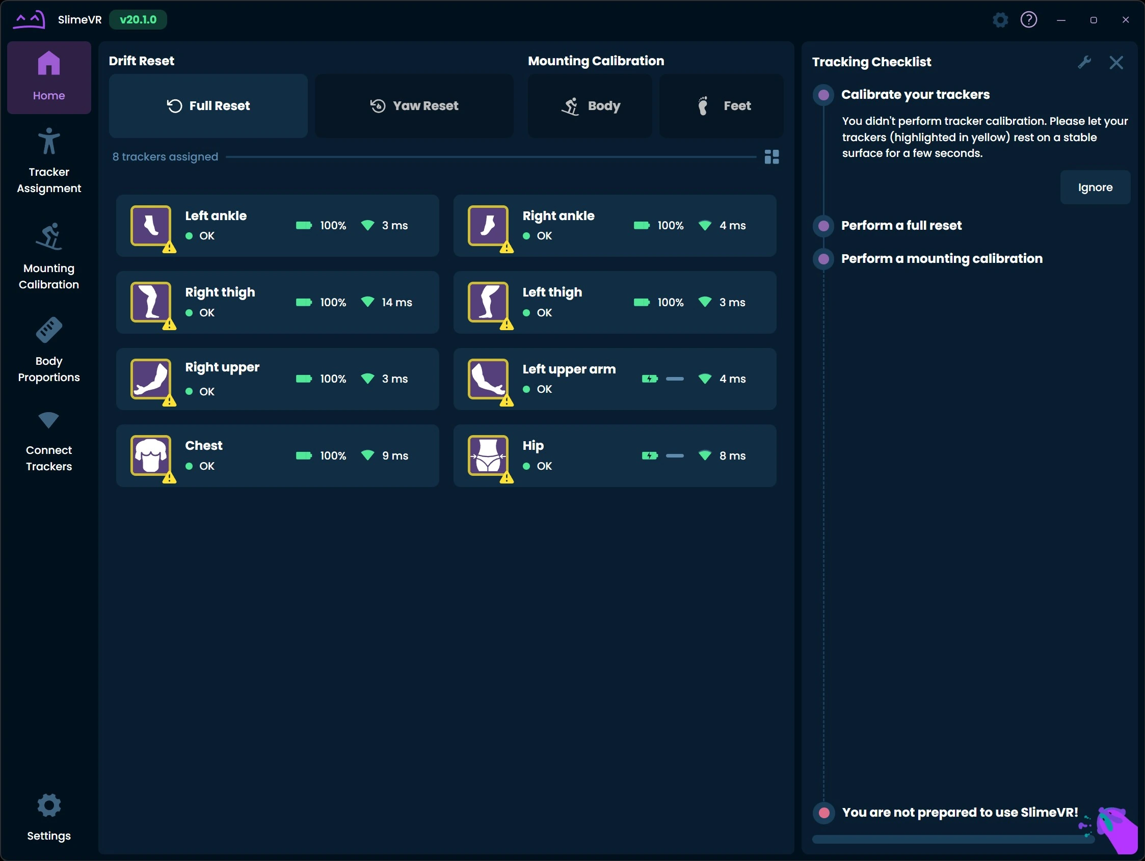
common/1-vrchat-use/images/slimevr-calibrate-your-trackers.webp
