OpenPawLabs/diy-guides/common/1-vrchat-use/images/slimevr-full-calibration-1.webp

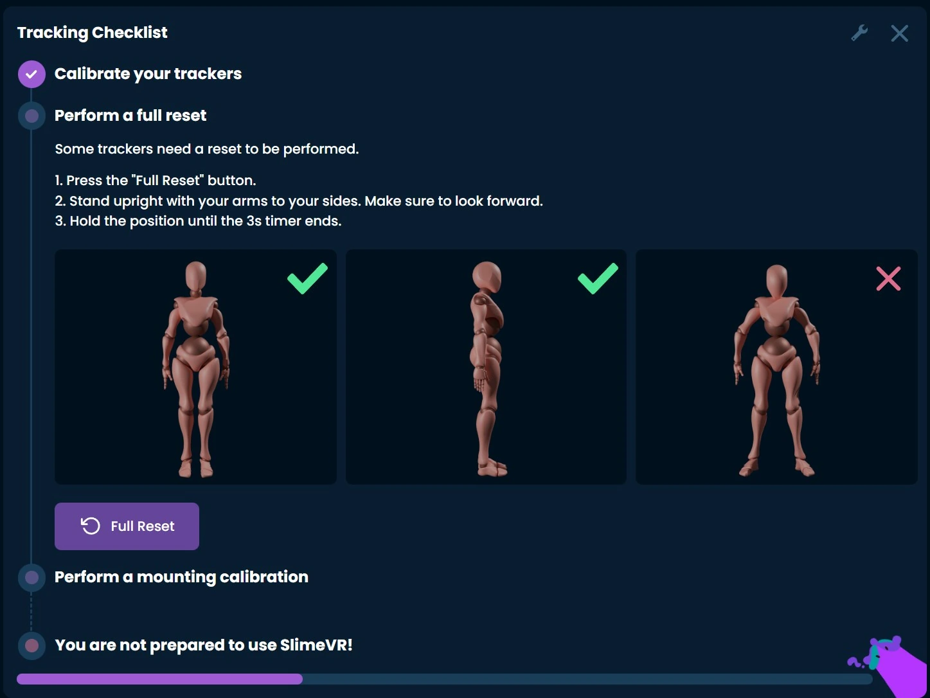
common/1-vrchat-use/images/slimevr-full-calibration-1.webp
