OpenPawLabs/diy-guides/common/1-vrchat-use/images/slimevr-mounting-calibration-2.webp

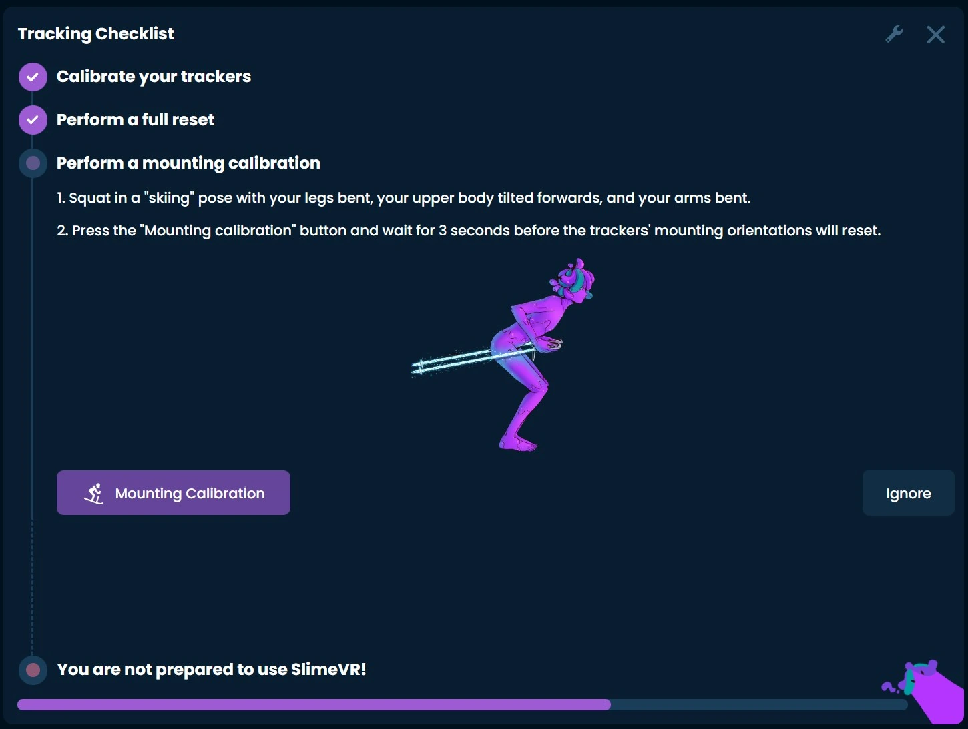
common/1-vrchat-use/images/slimevr-mounting-calibration-2.webp
