OpenPawLabs/diy-guides/common/1-vrchat-use/images/vrchat-calibration-mirror.webp

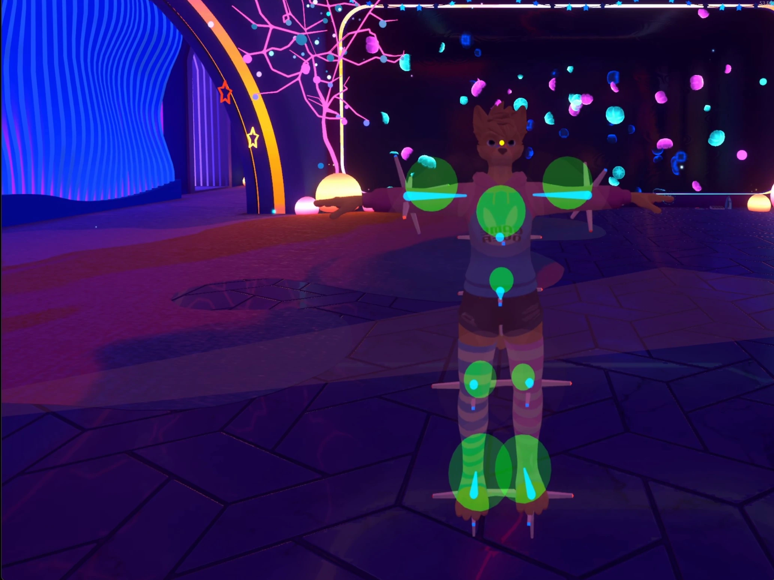
common/1-vrchat-use/images/vrchat-calibration-mirror.webp
