OpenPawLabs/diy-guides/common/1-vrchat-use/images/vrchat-wrist-menu-calibrate-button.webp

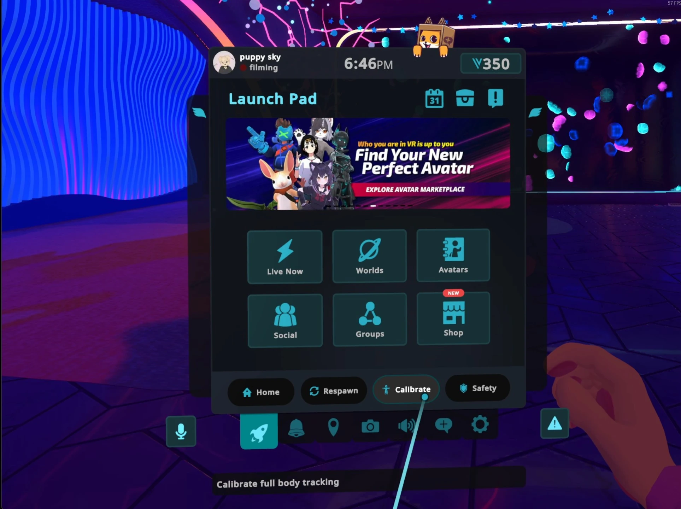
common/1-vrchat-use/images/vrchat-wrist-menu-calibrate-button.webp
